viniciushnf/ESP32-S3-Bruce-ST7735-1.8/wiring-diagram/display.png

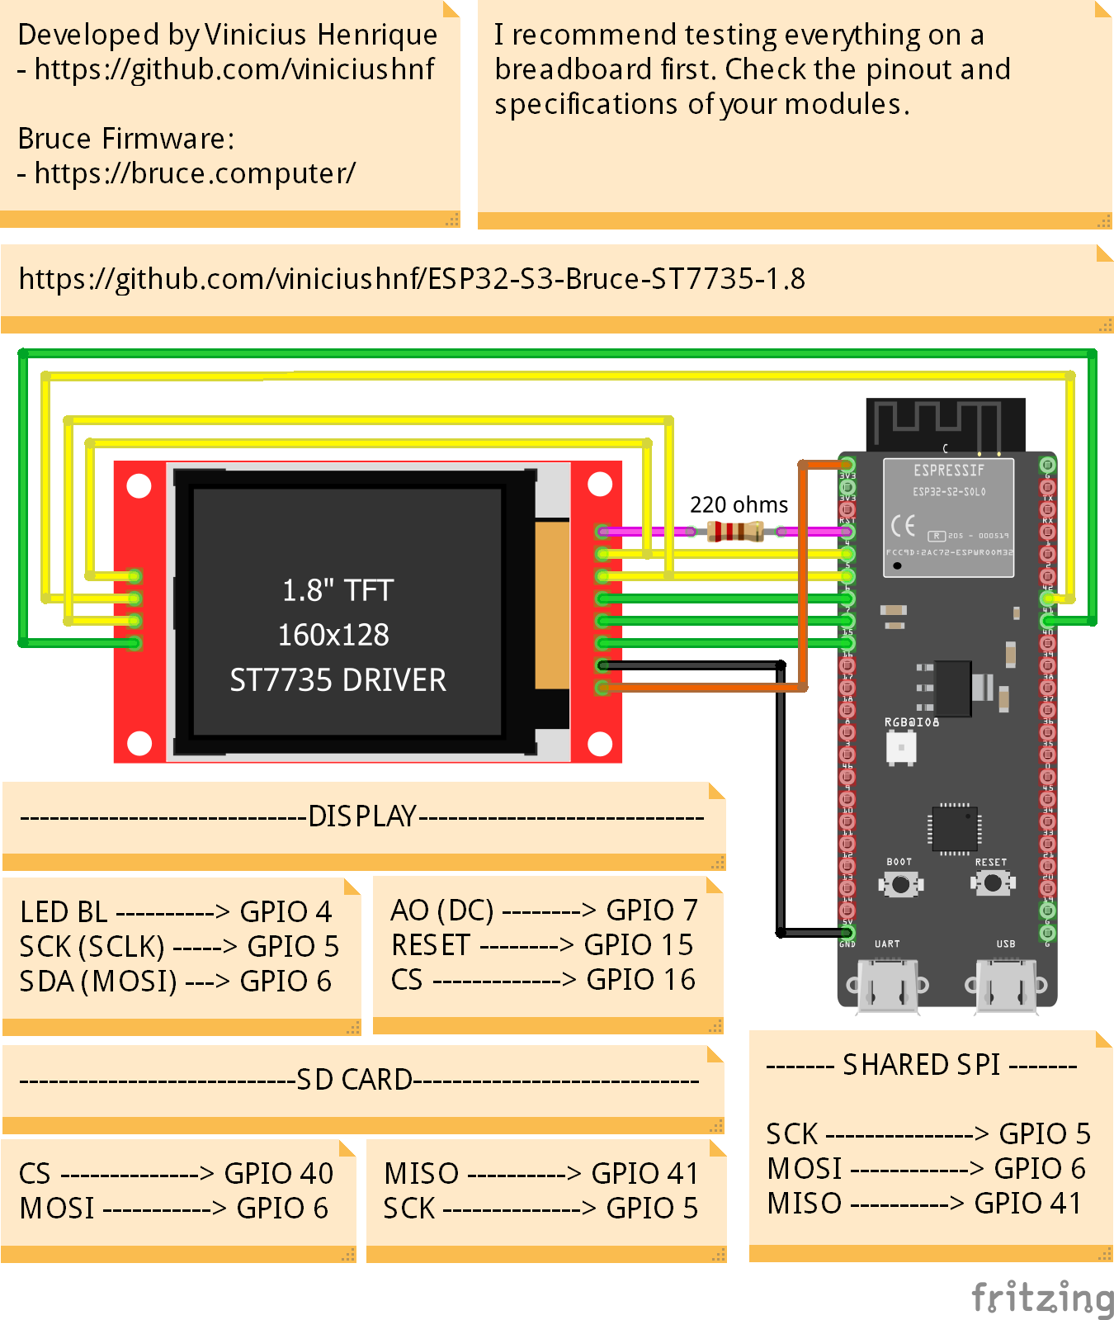
wiring-diagram/display.png
