viniciushnf/ESP32-S3-Bruce-ST7735-1.8/wiring-diagram/joystick.png

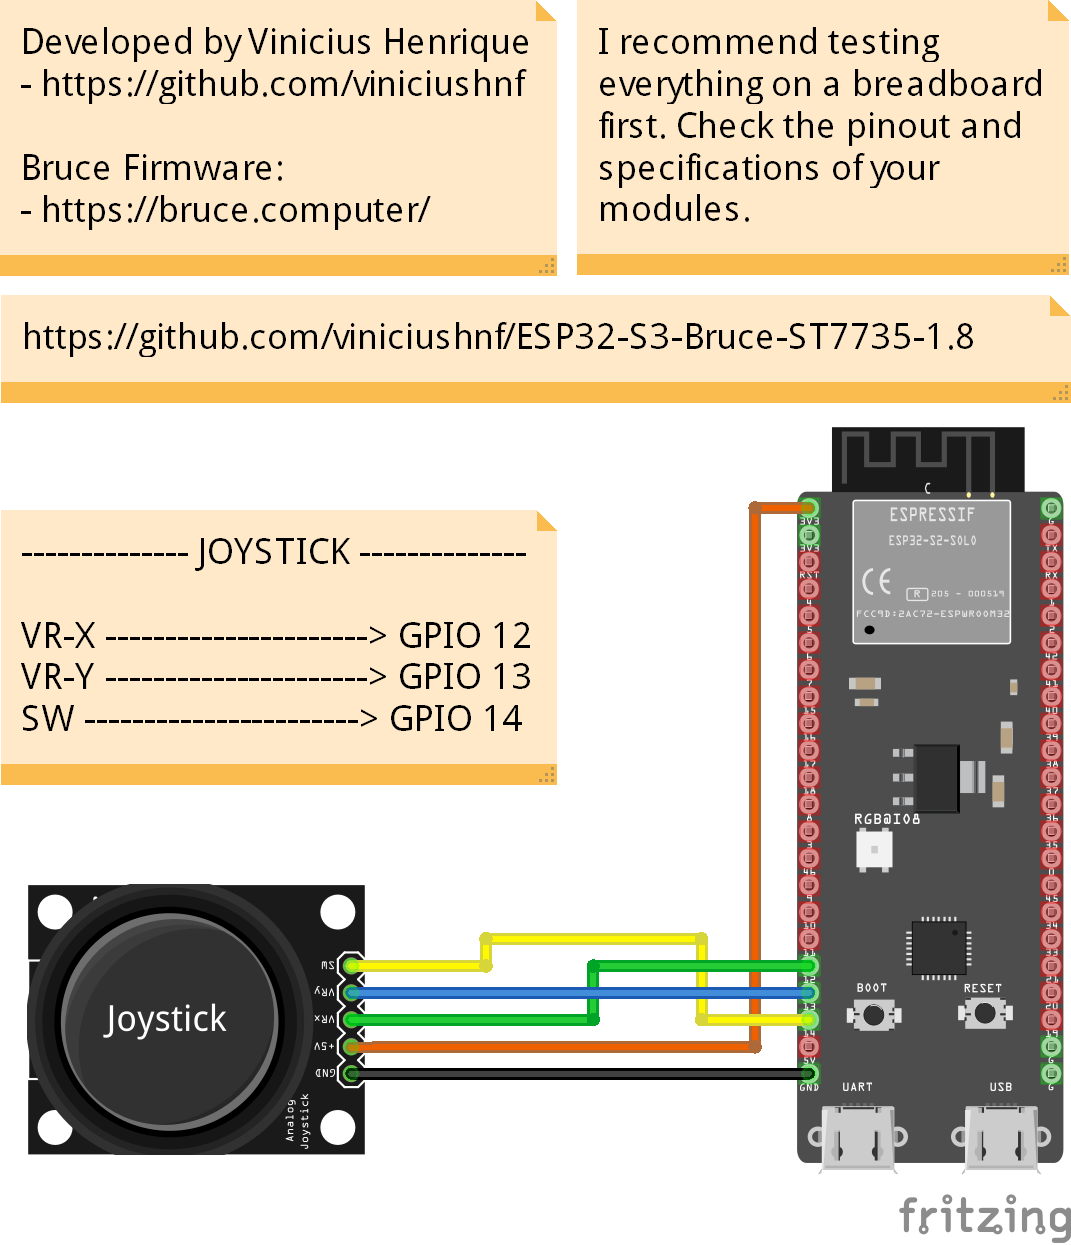
wiring-diagram/joystick.png
