viniciushnf/ESP32-S3-Bruce-ST7735-1.8/wiring-diagram/nrf24l01.png

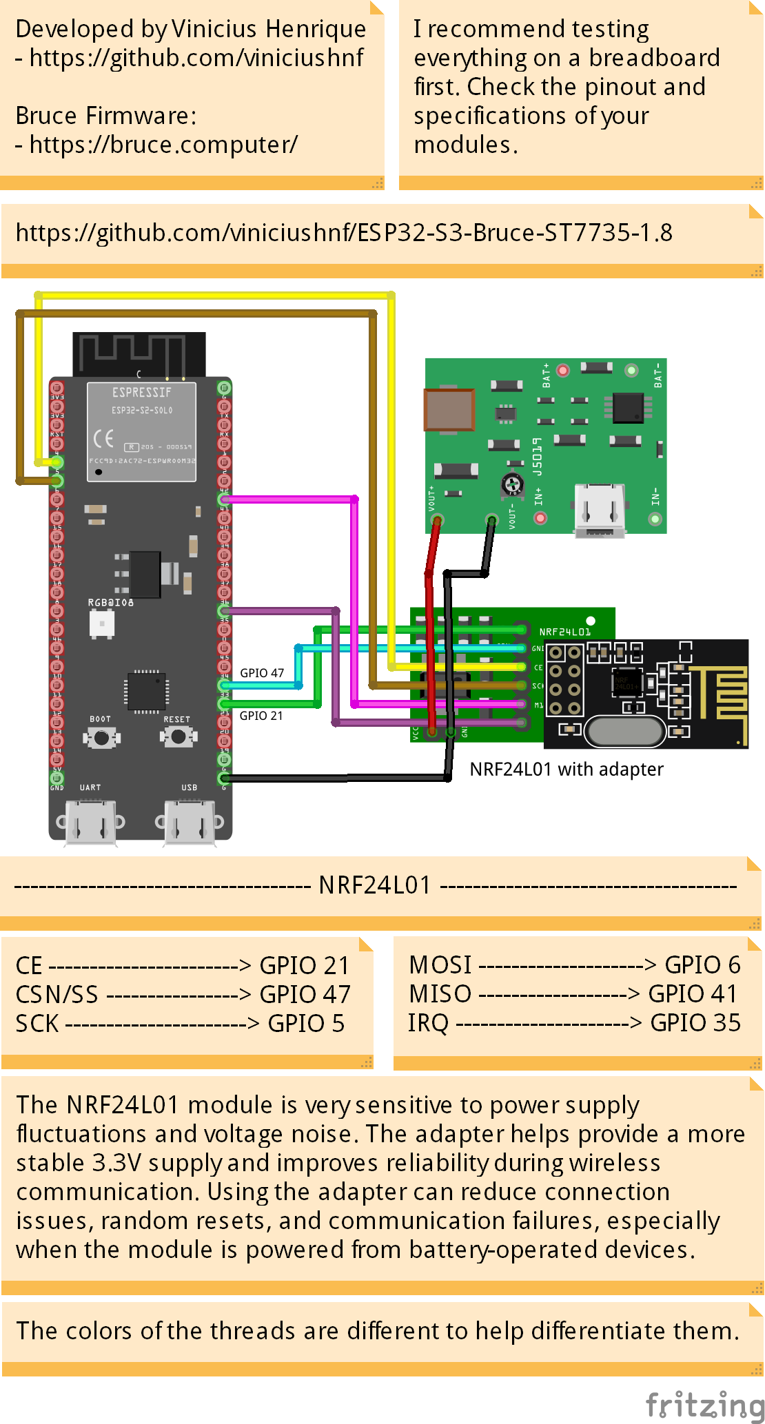
wiring-diagram/nrf24l01.png
