viniciushnf/ESP32-S3-Bruce-ST7735-1.8/wiring-diagram/pn532.png

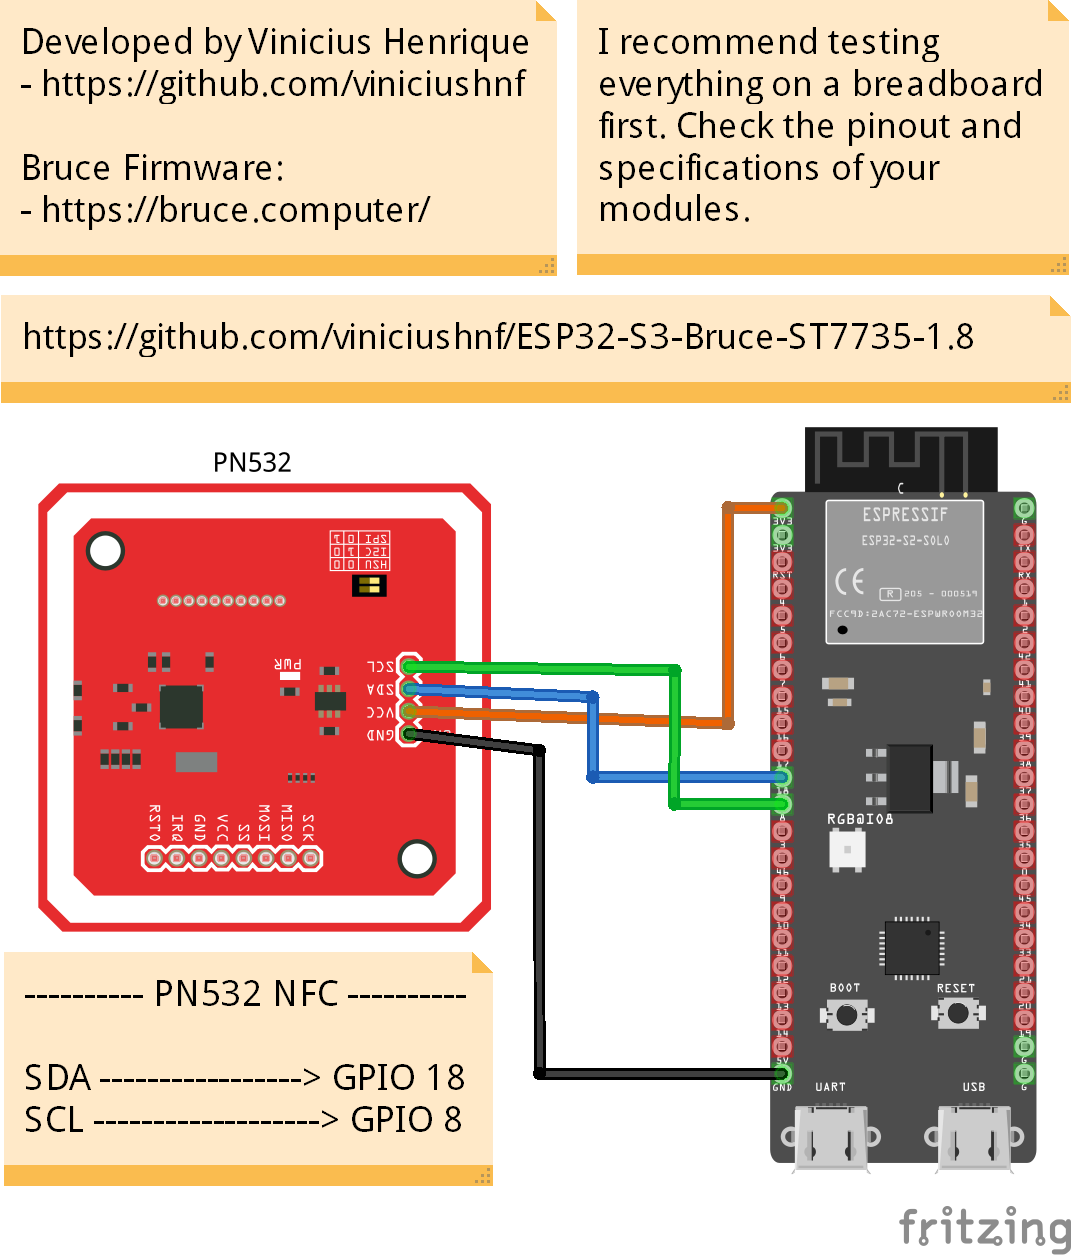
wiring-diagram/pn532.png
