viniciushnf/ESP32-S3-Bruce-ST7735-1.8/bruce-firmware/src/core/config.h

#ifndef __BRUCE_CONFIG_H__
#define __BRUCE_CONFIG_H__

#include "theme.h"
#include <Arduino.h>
#include <ArduinoJson.h>
#include <map>
#include <precompiler_flags.h>
#include <set>
#include <vector>

enum EvilPortalPasswordMode { FULL_PASSWORD = 0, FIRST_LAST_CHAR = 1, HIDE_PASSWORD = 2, SAVE_LENGTH = 3 };

class BruceConfig : public BruceTheme {
public:
    struct WiFiCredential {
        String ssid;
        String pwd;
    };
    struct Credential {
        String user;
        String pwd;
    };
    struct QrCodeEntry {
        String menuName;
        String content;
    };
    struct EvilPortalEndpoints {
        String getCredsEndpoint;
        String setSsidEndpoint;
        bool showEndpoints;
        bool allowSetSsid;
        bool allowGetCreds;
    };

    const char *filepath = "/bruce.conf";

    //  Settings
    int dimmerSet = 10;
    int bright = 100;
    bool automaticTimeUpdateViaNTP = true;
    float tmz = 0;
    bool dst = false;
    bool clock24hr = true;
    int soundEnabled = 1;
    int soundVolume = 100;
    int wifiAtStartup = 0;
    int instantBoot = 0;
    String keyboardLang = "QWERTY"; // "QWERTY" | "AZERTY" | "QWERTZ"

#ifdef HAS_RGB_LED
    // Led
    int ledBright = 50;
    uint32_t ledColor = 0x960064;
    int ledBlinkEnabled = 1;
    int ledEffect = 0;
    int ledEffectSpeed = 5;
    int ledEffectDirection = 1;
#endif

    // Wifi
    Credential webUI = {"admin", "bruce"};
    std::vector<String> webUISessions = {}; // FIFO queue of session tokens
    WiFiCredential wifiAp = {"BruceNet", "brucenet"};
    std::map<String, String> wifi = {};
    std::set<String> evilWifiNames = {};
    String wifiMAC = ""; //@IncursioHack

    // EvilPortal
    EvilPortalEndpoints evilPortalEndpoints = {"/creds", "/ssid", true, true, true};
    EvilPortalPasswordMode evilPortalPasswordMode = FULL_PASSWORD;

    void setWifiMAC(const String &mac) {
        wifiMAC = mac;
        saveFile(); // opcional, para salvar imediatamente
    }

    // RFID
    std::set<String> mifareKeys = {};

    // Misc
    String startupApp = "";
    String startupAppJSInterpreterFile = "";
    String wigleBasicToken = "";
    int devMode = 0;
    int colorInverted = 1;
    int badUSBBLEKeyboardLayout = 0;
    uint16_t badUSBBLEKeyDelay = 10;
    bool badUSBBLEShowOutput = true;

    std::vector<String> disabledMenus = {};

    std::vector<QrCodeEntry> qrCodes = {
        {"Bruce AP",   "WIFI:T:WPA;S:BruceNet;P:brucenet;;"},
        {"Bruce Wiki", "https://github.com/pr3y/Bruce/wiki"},
        {"Bruce Site", "https://bruce.computer"            },
        {"Rickroll",   "https://youtu.be/dQw4w9WgXcQ"      }
    };

    /////////////////////////////////////////////////////////////////////////////////////
    // Constructor
    /////////////////////////////////////////////////////////////////////////////////////
    BruceConfig() {};
    // ~BruceConfig();

    /////////////////////////////////////////////////////////////////////////////////////
    // Operations
    /////////////////////////////////////////////////////////////////////////////////////
    void saveFile();
    void fromFile(bool checkFS = true);
    void factoryReset();
    void validateConfig();
    JsonDocument toJson() const;

    // UI Color
    void setUiColor(uint16_t primary, uint16_t *secondary = nullptr, uint16_t *background = nullptr);

    // Settings
    void setDimmer(int value);
    void validateDimmerValue();
    void setBright(uint8_t value);
    void validateBrightValue();
    void setAutomaticTimeUpdateViaNTP(bool value);
    void setTmz(float value);
    void validateTmzValue();
    void setDST(bool value);
    void setClock24Hr(bool value);
    void setSoundEnabled(int value);
    void setSoundVolume(int value);
    void validateSoundEnabledValue();
    void validateSoundVolumeValue();
    void setWifiAtStartup(int value);
    void validateWifiAtStartupValue();

#ifdef HAS_RGB_LED
    // Led
    void setLedBright(int value);
    void validateLedBrightValue();
    void setLedColor(uint32_t value);
    void validateLedColorValue();
    void setLedBlinkEnabled(int value);
    void validateLedBlinkEnabledValue();
    void setLedEffect(int value);
    void validateLedEffectValue();
    void setLedEffectSpeed(int value);
    void validateLedEffectSpeedValue();
    void setLedEffectDirection(int value);
    void validateLedEffectDirectionValue();
#endif

    // Wifi
    void setWebUICreds(const String &usr, const String &pwd);
    void setWifiApCreds(const String &ssid, const String &pwd);
    void addWifiCredential(const String &ssid, const String &pwd);
    void addQrCodeEntry(const String &menuName, const String &content);
    void removeQrCodeEntry(const String &menuName);
    String getWifiPassword(const String &ssid) const;
    void addEvilWifiName(String value);
    void removeEvilWifiName(String value);
    void setEvilEndpointCreds(String value);
    void setEvilEndpointSsid(String value);
    void setEvilAllowEndpointDisplay(bool value);
    void setEvilAllowGetCreds(bool value);
    void setEvilAllowSetSsid(bool value);
    void setEvilPasswordMode(EvilPortalPasswordMode value);
    void validateEvilEndpointCreds();
    void validateEvilEndpointSsid();
    void validateEvilPasswordMode();

    // RFID
    void addMifareKey(String value);
    void validateMifareKeysItems();

    // Misc
    void setStartupApp(String value);
    void setStartupAppJSInterpreterFile(String value);
    void setWigleBasicToken(String value);
    void setDevMode(int value);
    void validateDevModeValue();
    void setColorInverted(int value);
    void validateColorInverted();
    void setBadUSBBLEKeyboardLayout(int value);
    void validateBadUSBBLEKeyboardLayout();
    void setBadUSBBLEKeyDelay(uint16_t value);
    void validateBadUSBBLEKeyDelay();
    void setBadUSBBLEShowOutput(bool value);
    void addDisabledMenu(String value);
    // TODO: removeDisabledMenu(String value);

    void addWebUISession(const String &token);
    void removeWebUISession(const String &token);
    bool isValidWebUISession(const String &token);
};

#endif
