viniciushnf/ESP32-S3-Bruce-ST7735-1.8/bruce-firmware/src/core/mykeyboard.cpp

#include "mykeyboard.h"
#include "core/utils.h"
#include "core/wifi/webInterface.h"
#include "modules/ir/TV-B-Gone.h"
#include "modules/ir/custom_ir.h"
#include "modules/rf/rf_send.h"
#include "powerSave.h"
#include "sd_functions.h"
#include <ArduinoJson.h>

int max_FM_size = tftWidth / (LW * FM) - 1;
int max_FP_size = tftWidth / (LW)-2;

// QWERTY KEYSET
const int qwerty_keyboard_width = 12;
const int qwerty_keyboard_height = 4;
char qwerty_keyset[qwerty_keyboard_height][qwerty_keyboard_width][2] = {
    //  4 lines, with 12 characters, capital and lowercase
    {{'1', '!'},
     {'2', '@'},
     {'3', '#'},
     {'4', '$'},
     {'5', '%'},
     {'6', '^'},
     {'7', '&'},
     {'8', '*'},
     {'9', '('},
     {'0', ')'},
     {'-', '_'},
     {'=', '+'} },
    {{'q', 'Q'},
     {'w', 'W'},
     {'e', 'E'},
     {'r', 'R'},
     {'t', 'T'},
     {'y', 'Y'},
     {'u', 'U'},
     {'i', 'I'},
     {'o', 'O'},
     {'p', 'P'},
     {'[', '{'},
     {']', '}'} },
    {{'a', 'A'},
     {'s', 'S'},
     {'d', 'D'},
     {'f', 'F'},
     {'g', 'G'},
     {'h', 'H'},
     {'j', 'J'},
     {'k', 'K'},
     {'l', 'L'},
     {';', ':'},
     {'"', '\''},
     {'|', '\\'}},
    {{'\\', '|'},
     {'z', 'Z'},
     {'x', 'X'},
     {'c', 'C'},
     {'v', 'V'},
     {'b', 'B'},
     {'n', 'N'},
     {'m', 'M'},
     {',', '<'},
     {'.', '>'},
     {'?', '/'},
     {'/', '/'} }
};

// AZERTY KEYSET (French)
const int azerty_keyboard_width = 12;
const int azerty_keyboard_height = 4;
char azerty_keyset[azerty_keyboard_height][azerty_keyboard_width][2] = {
    // Row 1: numbers / symbols
    {{'1', '&'},
     {'2', '\xc3'}, // é
     {'3', '"'},
     {'4', '\''},
     {'5', '('},
     {'6', '-'},
     {'7', '\xe8'}, // è
     {'8', '_'},
     {'9', '\xe7'}, // ç
     {'0', '\xe0'}, // à
     {')', '\xb0'},
     {'=', '+'}                      },
    // Row 2: AZERTY row
    {{'a', 'A'},
     {'z', 'Z'},
     {'e', 'E'},
     {'r', 'R'},
     {'t', 'T'},
     {'y', 'Y'},
     {'u', 'U'},
     {'i', 'I'},
     {'o', 'O'},
     {'p', 'P'},
     {'^', '\xa8'},                                       // ^ / ¨
     {'$', '\xa3'}}, // $ / £
    // Row 3: QSDFGH row
    {{'q', 'Q'},
     {'s', 'S'},
     {'d', 'D'},
     {'f', 'F'},
     {'g', 'G'},
     {'h', 'H'},
     {'j', 'J'},
     {'k', 'K'},
     {'l', 'L'},
     {'m', 'M'},
     {'\xf9', '%'},                                       // ù / %
     {'*', '\xb5'}}, // * / µ
    // Row 4: WXCVBN row
    {{'<', '>'},
     {'w', 'W'},
     {'x', 'X'},
     {'c', 'C'},
     {'v', 'V'},
     {'b', 'B'},
     {'n', 'N'},
     {',', '?'},
     {';', '.'},
     {':', '/'},
     {'!', '\xa7'},                                       // ! / §
     {'-', '_'}   }
};

// QWERTZ KEYSET (German)
const int qwertz_keyboard_width = 12;
const int qwertz_keyboard_height = 4;
char qwertz_keyset[qwertz_keyboard_height][qwertz_keyboard_width][2] = {
    // Row 1
    {{'1', '!'},
     {'2', '"'},
     {'3', '\xa7'}, // §
     {'4', '$'},
     {'5', '%'},
     {'6', '&'},
     {'7', '/'},
     {'8', '('},
     {'9', ')'},
     {'0', '='},
     {'\xdf', '?'},                          // ß / ?
     {'\'', '`'}                         },
    // Row 2: QWERTZ row
    {{'q', 'Q'},
     {'w', 'W'},
     {'e', 'E'},
     {'r', 'R'},
     {'t', 'T'},
     {'z', 'Z'},
     {'u', 'U'},
     {'i', 'I'},
     {'o', 'O'},
     {'p', 'P'},
     {'\xfc', '\xdc'},                       // ü / Ü
     {'+', '*'}                       },
    // Row 3: ASDF row
    {{'a', 'A'},
     {'s', 'S'},
     {'d', 'D'},
     {'f', 'F'},
     {'g', 'G'},
     {'h', 'H'},
     {'j', 'J'},
     {'k', 'K'},
     {'l', 'L'},
     {'\xf6', '\xd6'}, // ö / Ö
     {'\xe4', '\xc4'}, // ä / Ä
     {'#', '\''}},
    // Row 4: YXCVBN row
    {{'<', '>'},
     {'y', 'Y'},
     {'x', 'X'},
     {'c', 'C'},
     {'v', 'V'},
     {'b', 'B'},
     {'n', 'N'},
     {'m', 'M'},
     {',', ';'},
     {'.', ':'},
     {'-', '_'},
     {'/', '/'}                                             }
};

// HEX KEYSET
const int hex_keyboard_width = 4;
const int hex_keyboard_height = 4;
char hex_keyset[hex_keyboard_height][hex_keyboard_width][2] = {
    {{'0', '0'}, {'1', '1'}, {'2', '2'}, {'3', '3'}},
    {{'4', '4'}, {'5', '5'}, {'6', '6'}, {'7', '7'}},
    {{'8', '8'}, {'9', '9'}, {'A', 'a'}, {'B', 'b'}},
    {{'C', 'c'}, {'D', 'd'}, {'E', 'e'}, {'F', 'f'}},
};

// NUMBERS ONLY KEYSET
const int numpad_keyboard_width = 4;
const int numpad_keyboard_height = 3;
char numpad_keyset[numpad_keyboard_height][numpad_keyboard_width][2] = {
    // 3 lines, with 4 characters each:
    {{'1', '1'}, {'2', '2'}, {'3', '3'}, {'\0', '\0'}},
    {{'4', '4'}, {'5', '5'}, {'6', '6'}, {'.', '.'}  },
    {{'7', '7'}, {'8', '8'}, {'9', '9'}, {'0', '0'}  }
};

#if defined(HAS_TOUCH)
struct box_t {
    int x;
    int y;
    int w;
    int h;
    std::uint16_t color;
    int touch_id = -1;
    char key;
    char key_sh;

    void clear(void) {
        for (int i = 0; i < 8; ++i) { tft.fillRect(x, y, w, h, bruceConfig.bgColor); }
    }
    void draw(void) {
        int ie = touch_id < 0 ? 4 : 8;
        for (int i = 0; i < ie; ++i) {
            tft.drawRect(x, y, w, h, color);
            tft.setTextColor(color);
            tft.drawString(String(key), x + w / 2 - FM * LW / 2, y + h / 2 - FM * LH / 2);
        }
    }
    bool contain(int x, int y) {
        return this->x <= x && x < (this->x + this->w) && this->y <= y && y < (this->y + this->h);
    }
};

#endif

// Retrieves the current keyStroke from InputHandler, resets it after use.
// This function is used in loopTask to get the latest key press.
keyStroke _getKeyPress() {
#ifndef USE_TFT_eSPI_TOUCH
    vTaskSuspend(xHandle);
    keyStroke key = KeyStroke;
    KeyStroke.Clear();
    delay(10);
    vTaskResume(xHandle);
    return key;
#else
    keyStroke key = KeyStroke;
    KeyStroke.Clear();
    return key;
#endif
} // Returns a keyStroke that the keyboards won't recognize by default

/*********************************************************************
** Function: checkShortcutPress
** location: mykeyboard.cpp
** runs a function called by the shortcut action
**********************************************************************/
void checkShortcutPress() {
    static JsonDocument shortcutsJson; // parsed only once

    // lazy init
    if (shortcutsJson.size() == 0) {
        FS *fs;
        if (!getFsStorage(fs)) return;
        File file = fs->open("/shortcuts.json", FILE_READ);
        if (!file) {
            log_e("Shortcuts Config file not found. Using default values");
            JsonObject shortcuts = shortcutsJson.to<JsonObject>(); // root
            shortcuts["i"] = "loader open ir";
            shortcuts["r"] = "loader open rf";
            shortcuts["s"] = "loader open rf";
            shortcuts["b"] = "loader open badusb";
            shortcuts["w"] = "loader open webui";
            shortcuts["f"] = "loader open files";
            return;
        }
        // else
        if (deserializeJson(shortcutsJson, file)) {
            log_e("Failed to parse shortcuts.json");
            file.close();
            return;
        }
        file.close();
    }

    keyStroke key = _getKeyPress();

    // parse shortcutsJson and check the keys
    for (JsonPair kv : shortcutsJson.as<JsonObject>()) {
        const char *shortcut_key = kv.key().c_str();
        const char *shortcut_value = kv.value().as<const char *>();

        // check for matching keys
        for (auto i : key.word) {
            if (i == *shortcut_key) { // compare the 1st char of the key string
                // execute the associated action
                serialCli.parse(String(shortcut_value));
            }
        }
    }
}

/*********************************************************************
** Function: checkNumberShortcutPress
** location: mykeyboard.cpp
** return the pressed number
**********************************************************************/
int checkNumberShortcutPress() {
    // shortctus to quickly select options
    keyStroke key = _getKeyPress();
    for (auto i : key.word) {
        char c;
        for (c = '1'; c <= '9'; c++)
            if (i == c) return (c - '1');
    }
    // else
    return -1;
}

/*********************************************************************
** Function: checkLetterShortcutPress
** location: mykeyboard.cpp
** return the pressed letter
**********************************************************************/
char checkLetterShortcutPress() {
    // shortctus to quickly select options
    keyStroke key = _getKeyPress();
    for (auto i : key.word) {
        char c;
        for (c = 'a'; c <= 'z'; c++)
            if (i == c) return (c);
        for (c = 'A'; c <= 'Z'; c++)
            if (i == c) return (c);
    }
    // else
    return -1;
}

/*********************************************************************
** Shared keyboard helper functions
**********************************************************************/

/// Handles character deletion from the text string and screen
bool handleDelete(String &current_text, int &cursor_x, int &cursor_y) {
    if (current_text.length() == 0) return false;

    // remove from string
    current_text.remove(current_text.length() - 1);
    // delete from screen:
    int fontSize = FM;
    if (current_text.length() > max_FP_size) {
        tft.setTextSize(FP);
        fontSize = FP;
    } else tft.setTextSize(FM);
    tft.setCursor((cursor_x - fontSize * LW), cursor_y);
    tft.setTextColor(bruceConfig.priColor, bruceConfig.bgColor);
    tft.print(" ");
    tft.setTextColor(getComplementaryColor2(bruceConfig.bgColor), 0x5AAB);
    tft.setCursor(cursor_x - fontSize * LW, cursor_y);
    cursor_x = tft.getCursorX();
    cursor_y = tft.getCursorY();
    return true;
}

/// Handles adding a character to the text string
bool handleCharacterAdd(
    String &current_text, char character, int &cursor_x, int &cursor_y, const int max_size, bool mask_input
) {
    if (current_text.length() >= max_size) return false;

    current_text += character;
    if (current_text.length() != (max_FP_size + 1)) {
        if (mask_input) {
            tft.print("*");
        } else {
            tft.print(character);
        }
    }
    cursor_x = tft.getCursorX();
    cursor_y = tft.getCursorY();
    return true;
}

/// Handles adding space to the text string
bool handleSpaceAdd(String &current_text, const int max_size) {
    if (current_text.length() >= max_size) return false;
    current_text += ' ';
    return true;
}

// Enum for keyboard action results
enum KeyboardAction { KEYBOARD_CONTINUE, KEYBOARD_OK, KEYBOARD_CANCEL, KEYBOARD_REDRAW };
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
